Not-to-Shabby/TOMS/documentation/new_implementation_plan.md

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

---

## I. SLR Literature Analysis (TOMS.txt — Chapter II)

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

---

### A. Literature Challenges & TOMS Solutions

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

---

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

**TOMS approach — Real-time first, cache as fallback:**

```
Event occurs (NFC tap / payment / alarm)
        │
        ▼
  Internet available?
    YES ──► POST to server immediately (real-time occupancy)
    NO  ──► Write to local SQLite queue (synced = 0)
                    │
                    ▼
          Internet restored?
            YES ──► Flush SQLite queue (oldest first) + continue real-time
            NO  ──► Keep caching, retry every 30s
```

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

---

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

---

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

---

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

---

### B. Literature Research Gaps & TOMS Responses

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

---

### C. Occupancy — Does TOMS Align with the Literature?

**YES — and it fills the gap the literature couldn't.**

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

**TOMS fills this gap exactly:**

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

---

### D. Hardware Alignment with Literature (Table 2.9 / 2.10)

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

---

## II. Survey Problem Analysis & TOMS Solutions

The following maps each of the 7 identified field problems directly to TOMS features.

---

### Problem 1 — Inaccurate Passenger Counting
> *80% of conductors rely solely on memory or visual estimation*

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

---

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

**Root cause:** Conductors compute fares mentally while multitasking. Large bills create change-management stress.

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

---

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

---

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

**Root cause:** Paper tickets can be discarded. Verbal-only transactions leave no evidence.

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

---

### Problem 5 — Environmental Waste from Paper Tickets
> *90% agree paper tickets produce litter*

**Root cause:** Single-use paper tickets issued per passenger per trip.

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

---

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

**Root cause:** Routes pass through forested/rural areas with zero cellular signal.

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

---

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

**Root cause:** No digital record. Physical ticket collection is the only audit mechanism.

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

---

## II. Confirmed Architecture Decisions

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

---

## III. System Components

```
┌──────────────────────────────────────────────────────────────┐
│              COMPANY DASHBOARD (Web — browser)               │
│  Real-time fleet view, shift reports, audit trail, analytics │
│  Served from: Node.js or simple Python backend on office PC  │
│  Or: Static JSON export viewed in a local web app            │
└───────────────────────┬──────────────────────────────────────┘
                        │ Wi-Fi / USB sync (end of shift)
┌───────────────────────▼──────────────────────────────────────┐
│              FLUTTER APP (Conductor's Phone)                  │
│  Session mgmt • GPS • Fare calc • Proximity alarm            │
│  Offline SQLite log • Sync service                           │
└───────────────────────┬──────────────────────────────────────┘
                        │ USB CDC (always connected in-trip)
┌───────────────────────▼──────────────────────────────────────┐
│              ESP32 MASTER                                     │
│  NFC-DEP initiator (PN532) • ESP-NOW hub • SPIFFS backup    │
└────────────┬──────────────────────────────┬──────────────────┘
       NFC tap                          ESP-NOW
┌───────────▼──────────┐    ┌────────────▼──────────────────┐
│  SLAVE (NFC Target)  │    │  SLAVE (Button Press / Board) │
│  Shows QR receipt    │    │  PASSENGER_BOARD confirm      │
└──────────────────────┘    └───────────────────────────────┘
```

---

## IV. Occupancy Model

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

### Slot Number vs Seat Number

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

### Passenger States
```
ACTIVE    → BOARD_COMMAND sent, receipt on slave screen, payment pending
PAID      → passenger pressed button, fare collected, slave returned
ALARMING  → proximity alarm triggered, still unpaid
```

### Occupancy Flow
```
Trip starts. Bus has 0 slaves deployed. Capacity = 20.

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

Passenger 2 boards:
    → slot_number = 2
    → slavesDeployed = 2  →  Occupancy: 2/20 (10%)

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

GPS within 200m of Country Hills:
    → Slot 2 still unpaid → state = ALARMING
    → App banner + vibration
```

### `PassengerSlotState` enum (Flutter)
```dart
enum PassengerSlotState { active, paid, alarming }

extension PassengerSlotStateX on PassengerSlotState {
  Color get color => [
    const Color(0xFFFF9F43),   // active   → orange
    const Color(0xFF2ED573),   // paid     → green
    const Color(0xFFFF6B6B),   // alarming → red
  ][index];
  String get label => ['Unpaid', 'Paid', 'ALARM'][index];
}
```

### `OccupancySnapshot` (for dashboard sync)
```dart
class OccupancySnapshot {
  final String vehicleId;
  final DateTime timestamp;
  final int maxCapacity;          // configured max (e.g. 20)
  final int slavesDeployed;       // currently handed out
  final int paidCount;
  final int unpaidCount;
  final int alarmingCount;
  double get occupancyRate => slavesDeployed / maxCapacity;
  final List<PassengerSlot> slots;
}

class PassengerSlot {
  final int slotNumber;           // 1-based, order boarded
  final String slaveUid;          // eFuse MAC
  final PassengerSlotState state;
  final String destination;
  final int fareCentavos;
  final PassengerType passengerType;
  final DateTime boardedAt;
}
```

---

## V. Data Models

### `PassengerType` enum
```dart
enum PassengerType { regular, student, pwd, senior }

extension PassengerTypeX on PassengerType {
  String get label => ['Regular', 'Student', 'PWD', 'Senior'][index];
  double get multiplier => [1.0, 0.80, 0.80, 0.80][index];
}
```

### `TransitStop`
```dart
class TransitStop {
  final int id;
  final String name;
  final double lat;
  final double lon;
}
```
Loaded from `assets/stops.json` at startup.

### `PassengerSession`
```dart
class PassengerSession {
  final String id;              // UUID
  final String slaveUid;        // eFuse MAC of assigned slave
  final TransitStop boarding;
  final TransitStop destination;
  final int fareId;
  final int baseFareCentavos;
  final int finalFareCentavos;  // after discount
  final PassengerType type;
  final DateTime boardedAt;
  bool paid;
  bool alarmTriggered;
}
```

### `PendingPassenger` (Queue mode)
```dart
class PendingPassenger {
  final String id;
  final TransitStop boarding;
  final TransitStop destination;
  final int fareId;
  final int fareCentavos;
  final PassengerType type;
  final DateTime queuedAt;
}
```

### `PassengerLog` (updated)
```dart
// New fields added:
final int passengerType;        // PassengerType.index
final int discountCentavos;
final String boardingStop;
final String destinationStop;
final double destinationLat;
final double destinationLon;
```

### `DeviceStatus` (updated)
```dart
// Rename: uartState → nfcState
// Parse: json['nfc_state'] instead of json['uart_state']
final int nfcState;
```

### `ShiftReport` (new — for dashboard sync)
```dart
class ShiftReport {
  final String vehicleId;
  final String routeName;
  final DateTime shiftStart;
  final DateTime shiftEnd;
  final int totalPassengers;
  final int totalRevenueCentavos;
  final int regularCount;
  final int studentCount;
  final int pwdCount;
  final int seniorCount;
  final int discountTotalCentavos;
  final List<PassengerLog> transactions;
}
```

---

## V. Database Schema

**Version bump: `v1` → `v2`**

```sql
-- Migration from v1 to v2
ALTER TABLE passenger_logs ADD COLUMN passenger_type    INTEGER DEFAULT 0;
ALTER TABLE passenger_logs ADD COLUMN discount_centavos INTEGER DEFAULT 0;
ALTER TABLE passenger_logs ADD COLUMN boarding_stop     TEXT    DEFAULT '';
ALTER TABLE passenger_logs ADD COLUMN destination_stop  TEXT    DEFAULT '';
ALTER TABLE passenger_logs ADD COLUMN destination_lat   REAL    DEFAULT 0;
ALTER TABLE passenger_logs ADD COLUMN destination_lon   REAL    DEFAULT 0;
```

---

## VI. New Assets

### `assets/stops.json`
```json
[
  {"id":1, "name":"DPWH - Tambo Terminal",       "lat":8.2287, "lon":124.2451},
  {"id":2, "name":"Country Hills",               "lat":8.2456, "lon":124.2611},
  {"id":3, "name":"Brgy. Burul",                 "lat":8.2378, "lon":124.2534},
  {"id":4, "name":"Tag-ibo",                     "lat":8.1912, "lon":124.2133},
  {"id":5, "name":"Dalipuga Terminal",            "lat":8.1756, "lon":124.2089}
]
```
Operator populates the actual coordinates before deployment.

---

## VII. Services (Flutter)

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

### `SyncService` — Detailed Behaviour

```dart
class SyncService {
  // Called after every boarding event, payment, or alarm
  Future<void> push(OccupancyEvent event) async {
    // 1. Save to SQLite immediately (synced = 0)
    await _db.insertEvent(event);

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

  // Retry every 30 seconds while offline
  void startRetryTimer() {
    Timer.periodic(Duration(seconds: 30), (_) {
      if (_connectivity.isOnline) flushQueue();
    });
  }
}
```

**What is pushed to the server on each event:**
```json
{
  "event_type": "board",          // board | payment | alarm | release
  "timestamp": "2026-05-26T21:05:33+08:00",
  "vehicle_id": "CDB-001",
  "route": "Dalipuga",
  "slot_number": 3,
  "slave_uid": "A1B2C3D4E5F6",
  "passenger_type": "senior",
  "fare_centavos": 1040,
  "discount_centavos": 260,
  "boarding_stop": "DPWH Terminal",
  "destination_stop": "Country Hills",
  "occupancy_now": 14,             // slavesDeployed at time of event
  "max_capacity": 20
}
```

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

**Connectivity state indicator in UI:**
```
  🟢 Online   — events sent live to dashboard
  🟡 Caching  — N events queued, will sync on reconnect
  🔴 No USB   — master disconnected
```

### Discount Calculation
```dart
int calculateFare(int baseFareCentavos, PassengerType type) {
  return (baseFareCentavos * type.multiplier).ceil();
}
int calculateDiscount(int baseFareCentavos, PassengerType type) {
  return baseFareCentavos - calculateFare(baseFareCentavos, type);
}
```

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

---

## IX. Screens (Flutter App)

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

### New: `OccupancyPanel` (embedded in Dashboard, main widget)

No grid/seat map — just a capacity bar and a list of active passenger slot cards:
```
  CDB-001 · Dalipuga Route
  ┌────────────────────────────────────────────┐
  │ Occupancy  ████████████░░░░░░░░  14 / 20  │
  │            Unpaid: 3   Paid: 11   70%      │
  └────────────────────────────────────────────┘

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

  [ + New Passenger ]   Revenue today: ₱271.80
```

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

### New: `BoardingSheet` (Modal bottom sheet, 2 tabs)

**Tab 1 — Quick (Sequential)**
```
Boarding Point
  ○ Auto-GPS: [DPWH Terminal ✓ — detected]
  ○ Manual:   [Select stop ▾]

Destination:  [Country Hills ▾]
Passenger:    [Regular ▾]     → Fare: ₱13.00
                               → Discount: —

[Tap Slave via NFC]
```
- Auto-GPS pre-fills boarding stop from nearest stop to current phone position
- Selecting "Manual" shows the stop picker (searchable list)

**Tab 2 — Queue (Multi-passenger)**
```
Pending Queue
  □ DPWH → Country Hills  ₱13.00  Regular    [Assign →]
  □ DPWH → Brgy. Burol   ₱10.00  Senior ★   [Assign →]

[+ Add Another Passenger]
```
- "Assign →" taps that queue item's slave via NFC
- Multiple passengers can be queued before any slave is assigned

### New: `ActiveSessionsPanel` (on dashboard)
```
ACTIVE PASSENGERS  (3 riding · 2 unpaid)
┌─────────────────────────────────────────────────────┐
│ 🔴 S2  Country Hills    ₱10.40 Senior    UNPAID ⚠  │  ← alarm near
│ 🟡 S1  Brgy. Burol     ₱10.00 Regular   UNPAID    │
│ ✅ S3  Tambo Terminal  ₱ 9.00 Student   PAID      │
└─────────────────────────────────────────────────────┘
```
Each row: tap to expand → shows boarding time, slave UID, change calc

### New: `ProximityAlarmBanner`
```
⚠ UNPAID FARE — 150m to Country Hills
   Slave S2 · ₱10.40 Senior Citizen
                                    [Mark Paid]  [Dismiss]
```
+ Phone vibration + local notification sound

### New: `ShiftSummaryScreen`
Accessible from the overflow menu. Shows end-of-shift stats:
```
SHIFT SUMMARY  —  May 26, 2026

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

[ Export JSON ]   [ Sync to Dashboard ]
```

---

## IX. Company Dashboard (Web)

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

### Dashboard Screens

#### 1. Fleet Overview (Home) — with Live Occupancy
```
TOMS Fleet Dashboard — DATRANSCO                  May 26, 2026

Active Buses: 3    Fleet Avg Occupancy: 61%    Total Revenue Today: ₱4,230.00

┌──────────┬──────────┬───────────┬──────────────────────┬──────────┬──────────┐
│ Bus ID   │ Route    │ Conductor │ Occupancy            │ Revenue  │ Status   │
├──────────┼──────────┼───────────┼──────────────────────┼──────────┼──────────┤
│ CDB-001  │ Dalipuga │ J. Reyes  │ ████████░░  14/20    │ ₱168.00  │ 🟢 Live  │
│ CDB-002  │ Dalipuga │ R. Santos │ █████░░░░░   9/20    │ ₱109.00  │ 🟡 Sync  │
│ CDB-003  │ Buru-un  │ M. Cruz   │ ████████████ 20/20   │ ₱240.00  │ 🟢 Live  │
└──────────┴──────────┴───────────┴──────────────────────┴──────────┴──────────┘
```
- **Occupancy** = slaves deployed / bus max capacity
- **🟢 Live** = events received in real-time (phone has internet)
- **🟡 N cached** = phone offline, N events queued — occupancy shown is last known state
- Click any row → opens per-bus **passenger slot list** (mirrors conductor's phone panel)
- `20/20` (FULL) highlighted — dispatcher knows to send the next bus
- Occupancy updates immediately as events arrive; no manual refresh needed

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

#### 3. Revenue Analytics
```
Revenue Trends — Last 7 Days

₱5,000 ┤                              ╭───╮
₱4,000 ┤              ╭──╮           │   │
₱3,000 ┤    ╭──╮     │  ╰──╮       ╭╯   ╰─
₱2,000 ┤───╯  ╰─────╯     ╰──────╯
       Mon   Tue   Wed   Thu   Fri   Sat   Sun

Passenger Type Breakdown:
  Regular  78%   ████████████████████░░░░░
  Student  12%   ████░░░░░░░░░░░░░░░░░░░░░
  Senior    7%   ██░░░░░░░░░░░░░░░░░░░░░░░
  PWD       3%   █░░░░░░░░░░░░░░░░░░░░░░░░
```

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

#### 5. Reconciliation Report (replaces the 6 PM office visit)
```
End-of-Day Reconciliation — May 26, 2026

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

Bus CDB-002 (Buru-un):
  Expected passengers:  18
  Expected revenue:   ₱214.50
  Cash declared:      ₱200.00  ⚠ DISCREPANCY: -₱14.50
  Status: ❌ REVIEW REQUIRED
```

### Dashboard Tech Stack Options

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

---

## X. Flutter Packages Required

```yaml
# pubspec.yaml additions
geolocator: ^13.0.1              # Phone GPS
permission_handler: ^11.3.0      # Location + notification permissions
vibration: ^3.1.2                # Haptic alarm
flutter_local_notifications: ^17.2.2  # Audible alarm
share_plus: ^10.0.2              # Export shift JSON / CSV
http: ^1.2.0                     # Real-time event POST + sync queue flush
uuid: ^4.4.0                     # Session ID generation
connectivity_plus: ^6.0.3        # Internet state monitoring (online/offline)
```

---

## XI. Protocol Extension (Firmware, Phase 4 Only)

### New: `TOMS_MSG_ALARM_CMD` (Master → Slave)

Add to `shared_lib/protocol/protocol.h`:
```c
TOMS_MSG_ALARM_CMD = 0x30,

typedef struct __attribute__((packed)) {
    uint8_t  target_uid[16];
    uint8_t  alarm_type;      // 0 = proximity warning, 1 = final stop
    uint8_t  minutes_left;
} toms_alarm_cmd_t;
```

Master USB handler — new command from phone:
```json
{"cmd":"send_alarm", "uid":"A1B2C3D4E5F6", "alarm_type":0, "minutes":2}
```

Slave response: Flash screen red → "Please Pay — 2 min to stop"

---

## XIII. Build Phases

### Phase 1 — NFC + Occupancy Foundation (Flutter only)
- [ ] Update `DeviceStatus`: `uartState` → `nfcState`
- [ ] Add `PassengerType`, `TransitStop`, `PassengerSession`, `PendingPassenger` to models
- [ ] Add `SeatState`, `SeatRecord`, `OccupancySnapshot` to models
- [ ] Add `NfcTapEvent` model
- [ ] Database v2 migration (add columns)
- [ ] `OccupancyService` — seat state table, update from NFC tap + button_press + proximity
- [ ] `SessionService` (sessions + queue + fare calc + discounts)
- [ ] `UsbService` NFC event handlers (replace dock with nfc/nfc_tap)
- [ ] `AppState` wired to OccupancyService + SessionService + button_press → markPaid

### Phase 2 — Occupancy Panel + Boarding UI
- [ ] `assets/vehicles.json` — max capacity per bus ID (simple: `{"CDB-001": 20, ...}`)
- [ ] `assets/stops.json` (named stops + GPS coords)
- [ ] `StopService` (load + find nearest stop)
- [ ] **`OccupancyPanel`** — capacity bar + `PassengerSlot` card list, embedded in Dashboard
- [ ] Slot number auto-increment logic in `SessionService` (resets each trip)
- [ ] [Release Slave] action → frees slot, slave returned to pool
- [ ] `BoardingSheet` — Quick tab (GPS auto-boarding + stop picker + discount selector)
- [ ] `BoardingSheet` — Queue tab (multi-passenger queue)
- [ ] `ShiftSummaryScreen` with occupancy stats (peak occupancy, avg load, etc.)
- [ ] NFC tap → BOARD_COMMAND with `slot_number` (reused `seat_number` field) + fare + type

### Phase 3 — GPS + Proximity Alarm
- [ ] `GpsService` with `geolocator`
- [ ] `ProximityService` — 200m geofence, updates seat state to ALARMING
- [ ] Seat map tile pulses red when ALARMING
- [ ] `ProximityAlarmBanner` with [Mark Paid] action
- [ ] Vibration + local notification
- [ ] Android permissions: `ACCESS_FINE_LOCATION`, `VIBRATE`, `POST_NOTIFICATIONS`

### Phase 4 — Company Dashboard + Sync
- [ ] `SyncService` — export `OccupancySnapshot` + `ShiftReport` JSON
- [ ] Company dashboard (HTML/JS)
  - Fleet overview with live occupancy bars per bus
  - Per-bus seat map view (mirrors conductor's phone)
  - Transaction audit log (searchable)
  - Revenue analytics (per day/week, passenger type breakdown)
  - Reconciliation report (auto-flags discrepancy)
  - Dispute resolution search by UID / timestamp
- [ ] `share_plus` — conductor shares shift JSON at terminal

### Phase 5 — Slave Alarm (Firmware, Optional)
- [ ] `TOMS_MSG_ALARM_CMD` in `protocol.h`
- [ ] Slave: alarm cmd → red screen + "Please Pay" UI
- [ ] Master: `send_alarm` USB cmd → ESP-NOW to target slave
- [ ] Flutter `ProximityService` triggers slave alarm alongside phone alarm
