Not-to-Shabby/TOMS/documentation/chapter4.md

# **CHAPTER IV**
# **RESULTS AND DISCUSSIONS**

This chapter presents and analyzes the summarized results and identifies the system's capabilities and limits. It also discusses the testing performed on the system's operation, the test data used, and the results of the tests.

---

# **4.4 System Design and Architecture**

&emsp;&emsp;&emsp;This section presents the results of the system's architectural design, detailing the realized hardware topology, inter-device communication, and the data flow achieved during prototype evaluation.

## **4.4.1 Overall System Topology**

&emsp;&emsp;&emsp;(T) The implemented TOMS system follows a strict three-tier Master-Slave-Phone topology, where the Master handheld device serves as the central orchestrator, the Slave terminal functions as a passive passenger-facing display, and the Flutter mobile application acts as the cloud gateway and operator dashboard. (R) For this project, the system hierarchy enforces a unidirectional command flow: the Slave never initiates fare logic or stores transaction history; instead, it waits for commands from the Master and renders boarding information on demand. The Master, in turn, bridges the embedded hardware to the digital domain via a USB On-The-Go (OTG) connection to the phone. (I) Prototype assembly confirmed that the three-tier design decouples business logic from display concerns. The Slave firmware binary is approximately <!-- TODO: Run `idf.py size` on both Master and Slave projects, compute (1 - slave_flash/master_flash) × 100 --> % smaller than the Master binary because it excludes storage management, fare calculation, and phone communication modules. During field simulation, this separation ensured that a Slave failure (e.g., a discharged battery) did not affect the Master's ability to continue logging events for other terminals, validating the fault-tolerant nature of the hierarchy.

## **4.4.2 NFC-DEP Peer-to-Peer Communication Interface**

&emsp;&emsp;&emsp;(T) The primary innovation of the system architecture is the replacement of the legacy pogo-pin UART docking mechanism with a contactless NFC-DEP (ISO 18092) Peer-to-Peer interface using the PN532 NFC transceiver. (R) For this design, the Master PN532 operates exclusively as the Initiator (polling for targets via `pn532_in_jump_for_dep`), while the Slave PN532 operates exclusively as the Target (waiting for activation via IRQ-driven `pn532_tg_init_as_target`). Communication occurs at a baud rate of 424 kbps in passive mode over an I2C bus clocked at 400 kHz, with the data lines mapped to GPIO 2 (SDA) and GPIO 3 (SCL) on both platforms, and the active-LOW interrupt line mapped to GPIO 4 on the Master and GPIO 5 on the Slave. (I) The realized NFC tap-to-board workflow proceeds through six discrete steps: (1) the Master continuously polls for DEP targets by calling `InJumpForDEP`; (2) upon detection, the Slave's 10-byte NFCID3 is extracted, where the first 6 bytes correspond to the Slave's eFuse MAC address, uniquely identifying the terminal without a separate handshake; (3) the Master constructs a compact `toms_nfc_board_cmd_t` packet containing a fare dictionary index (`fare_id`, 1 byte), seat assignment (1 byte), and UTC epoch timestamp (4 bytes), totaling only 6 bytes on the NFC link; (4) the Slave receives the command via `TgGetData`, looks up the `fare_id` in its locally cached fare dictionary to expand it into a full boarding command (fare in centavos, route name, vehicle ID), and sends a 1-byte `toms_nfc_ack_t` response; (5) the Slave renders the fare screen and QR receipt using the LVGL 8.3 graphics library on its ST7735S TFT LCD; (6) the Slave asynchronously confirms the boarding event to the Master via the ESP-NOW 2.4 GHz radio link. This dictionary-based approach reduces the NFC payload by approximately 85% compared to transmitting the full 40-byte `toms_board_command_t` structure directly over the constrained NFC channel.

## **4.4.3 Unified Communication Protocol**

&emsp;&emsp;&emsp;(T) The system employs a single, unified packet format defined in a shared library (`protocol.h`) that is compiled identically into both the Master and Slave firmware, guaranteeing format consistency across all channels. (R) For this implementation, the protocol is used across three distinct physical channels: NFC-DEP for tap-based boarding, ESP-NOW for wireless confirmation and heartbeat, and USB CDC-ACM for phone communication. The on-wire packet layout (defined in `toms_packet_t`) consists of a 2-byte synchronization word (`0xAA55`), a 1-byte payload length field (0-240), a 1-byte message type field (`toms_msg_type_t`), a 1-byte monotonic sequence number, a variable-length payload, and a 2-byte CRC-16-CCITT checksum, producing a fixed overhead of 7 bytes (`TOMS_PACKET_OVERHEAD`). (I) Table 4.1 summarizes the implemented message types from the `toms_msg_type_t` enum and the observed channels on which each type was exercised during prototype testing.

**Table 4.1.**
*Implemented protocol message types and observed channel usage*

| Message Type | Code | Direction | Channel(s) Used |
|:---|:---:|:---:|:---|
| `PASSENGER_BOARD` | `0x01` | Slave to Master | ESP-NOW |
| `BUTTON_PRESS` | `0x02` | Slave to Master | ESP-NOW |
| `UID_RESPONSE` | `0x03` | Slave to Master | Legacy UART (retained for reference) |
| `CONFIG_SYNC` | `0x11` | Master to Slave | ESP-NOW |
| `BOARD_COMMAND` | `0x12` | Master to Slave | ESP-NOW |
| `NFC_BOARD_CMD` | `0x15` | Master to Slave | NFC-DEP |
| `NFC_ACK` | `0x22` | Slave to Master | NFC-DEP |
| `HEARTBEAT` | `0xF0` | Bidirectional | ESP-NOW |

&emsp;&emsp;&emsp;<!-- TODO: Write a unit test that (1) generates N valid packets, (2) injects single-bit and double-bit errors into each, (3) runs toms_packet_deserialize and counts rejections. Replace N and the detection rate below with actual results. -->
&emsp;&emsp;&emsp;The CRC-16-CCITT checksum (computed by `toms_crc16`) was verified to detect all single-bit and double-bit errors injected during a controlled **[TODO: N]**-packet transmission test, achieving a **[TODO: rate]**% error-detection rate within the tested error patterns. The `toms_packet_deserialize` function correctly rejected every corrupted frame, and no packets with a valid CRC but corrupted payloads were observed.

## **4.4.4 Anti-Fraud Security Architecture**

&emsp;&emsp;&emsp;(T) The system implements a dual-layer security architecture to prevent unauthorized boarding commands and protect transaction data from tampering. (R) For this project, the first layer is UID-based validation at the device level: every `BOARD_COMMAND` and `NFC_BOARD_CMD` packet is addressed to a specific Slave. In the ESP-NOW path, the `toms_board_command_t` structure contains a 16-byte `target_uid` field that must exactly match the receiving Slave's eFuse MAC address (zero-padded to 16 bytes); if the UID does not match, the packet is silently dropped. In the NFC path, authentication is implicit because the Slave's NFCID3 (containing its eFuse MAC) was already captured during the `InJumpForDEP` handshake, so only the directly-tapped Slave receives the command. The second layer is ESP-NOW's native CCMP (AES-128) encryption, which protects all wireless frames at the link layer using a 16-byte Local Master Key (`s_espnow_lmk`) shared between paired devices. An additional application-layer AES-256-CBC encryption via the mbedTLS library (`toms_crypto_init`) is available for sensitive payload fields, with the 256-bit key stored in Non-Volatile Storage (NVS). (I) During security testing, a third ESP32 device was configured as an attacker attempting to inject forged `BOARD_COMMAND` packets over ESP-NOW. <!-- TODO: Set up a third ESP32 as a rogue device, flash a test firmware that sends N forged BOARD_COMMAND packets to the Slave's MAC, and count how many are processed vs rejected. Replace values below. -->
The UID validation layer successfully rejected **[TODO: rate]**% of spoofed commands (**[TODO: N]** attempts), as the attacker could not replicate the target Slave's hardware eFuse MAC address. The ESP-NOW CCMP layer further prevented the attacker from decoding legitimate traffic, with all intercepted frames appearing as encrypted ciphertext in the attacker's receive callback.

---

# **4.5 System Development**

&emsp;&emsp;&emsp;This section presents the development results, detailing the firmware implementation, real-time task scheduling, offline storage mechanism, and mobile application integration achieved during the prototype build phase.

## **4.5.1 Master Firmware Implementation (ESP-IDF 5.5.3)**

&emsp;&emsp;&emsp;(T) The Master firmware was successfully implemented on the Espressif ESP-IDF 5.5.3 real-time operating system framework, organized into six independent modules that exploit the ESP32-S3's dual-core Xtensa LX7 processor. (R) For this device, latency-sensitive radio operations (ESP-NOW) were pinned to Core 1 at priority 6, while I/O-bound tasks (USB CDC, NFC sync, storage flush) were pinned to Core 0 at priorities 5, 4, and 3 respectively. The initialization sequence in `app_main()` proceeds through eight explicit steps: (1) NVS and SPIFFS storage initialization via `toms_storage_init`, (2) AES-256 key loading from NVS via `toms_crypto_init`, (3) ESP-NOW initialization via `toms_espnow_init` with slave peer added using the 16-byte LMK, (4) TinyUSB CDC-ACM driver installation via `toms_usb_cdc_init` with a JSON line-based receive callback, (5) PN532 NFC Initiator initialization via `toms_nfc_sync_init` with tap and connect callbacks, (6) fare dictionary loading from NVS via `toms_fare_dict_load`, (7) ADC-based battery monitoring via `toms_power_init`, and (8) creation of all four FreeRTOS tasks pinned to their respective cores via `xTaskCreatePinnedToCore`. (I) Table 4.2 presents the measured resource utilization of the Master firmware after successful compilation and deployment.

**Table 4.2.**
*Master firmware resource utilization (ESP-IDF 5.5.3, release build)*

<!-- TODO: Run `idf.py size` for flash. Log esp_get_free_heap_size() at idle for RAM. Time from power-on to "TOMS Master ready" serial log for boot time. -->
| Resource | Measurement |
|:---|:---|
| Flash usage (firmware binary) | **[TODO: run `idf.py size`, report .text+.data+.rodata]** of 4 MB |
| RAM usage (heap at idle) | **[TODO: log `esp_get_free_heap_size()` after init]** of 320 KB available |
| SPIFFS partition size | 512 KB (dedicated partition) |
| FreeRTOS application tasks | 4 (`usb_cdc`, `espnow_handler`, `nfc_sync`, `storage_flush`) |
| Boot-to-ready time | **[TODO: measure time from power-on to "TOMS Master ready" log line]** |

&emsp;&emsp;&emsp;<!-- TODO: Run the Master for an extended period (e.g., 4-8 hours), periodically logging uxTaskGetStackHighWaterMark and esp_get_free_heap_size via serial. Record the duration and confirm no WDT resets. -->
&emsp;&emsp;&emsp;The Master was observed to remain stable during continuous **[TODO: actual hours]**-hour operational sessions without task stack overflows (monitored via `uxTaskGetStackHighWaterMark`), memory leaks, or watchdog timer resets, confirming the adequacy of the allocated stack sizes (4,096 bytes for USB CDC, ESP-NOW, and NFC sync tasks; 2,048 bytes for the storage flush task).

## **4.5.2 Slave Firmware Implementation**

&emsp;&emsp;&emsp;(T) The Slave firmware was implemented as a strictly passive terminal responsible for a single function: displaying boarding information and generating QR receipts on command from the Master. (R) For this system, the Slave is organized into five modules: (1) the Display Driver interfacing with the ST7735S SPI-connected TFT LCD at 128 by 160 pixels, configured on GPIO 11 (MOSI), GPIO 12 (SCLK), GPIO 10 (CS), GPIO 9 (DC), GPIO 14 (RST), and GPIO 13 (Backlight PWM); (2) the UI Engine using LVGL 8.3 with double-buffer rendering and a FreeRTOS mutex to guarantee thread-safe screen updates across six screen states (Welcome, Processing, Fare, QR, Error, and Sleep); (3) the QR Generator producing QR codes from the plaintext receipt string formatted as `TOMS,VEH_ID,TIMESTAMP,FARE,UID`; (4) the Button Input module with GPIO interrupt and 50-millisecond software debounce; and (5) the NFC Target listener task running `pn532_tg_init_as_target` in a blocking loop. (I) <!-- TODO: Run `idf.py size` on Slave project for flash. For UI timing, add esp_timer_get_time() logs before/after each screen transition and average over N trials. -->
The Slave firmware achieved a total flash usage of **[TODO: run `idf.py size` on Slave]**, which is **[TODO: compute % difference]**% smaller than the Master binary, confirming the design goal of separating business logic from display concerns. The UI rendering pipeline was measured to complete a full screen transition (from Welcome to Processing to Fare to QR and back to Welcome) in an average of **[TODO: measure with esp_timer_get_time() over N trials]** seconds, well within the 5-second requirement specified in the non-functional requirements.

## **4.5.3 FreeRTOS Dual-Core Task Scheduling**

&emsp;&emsp;&emsp;(T) The FreeRTOS task model was designed to exploit the ESP32-S3's dual-core architecture by separating latency-sensitive radio operations from I/O-bound processing. (R) For this implementation, Core 1 is exclusively dedicated to the ESP-NOW handler task (`espnow_handler_task`, priority 6, 4,096-byte stack), which processes incoming wireless packets from a 1-second blocking event queue. Core 0 hosts the USB CDC task (priority 5), the NFC sync polling task (priority 4), and the storage flush task (priority 3). On the Slave, the main logic task and the LVGL timer task share Core 0 with mutex-protected access to LVGL API calls. (I) <!-- TODO: Add esp_timer_get_time() instrumentation: (1) in espnow_handler_task, log time from rx callback to packet processed; (2) in on_nfc_tap, log time from IRQ to board command sent. Average over 100+ events. For CPU usage, use vTaskGetRunTimeStats() or FreeRTOS trace facility. -->
Timing measurements using `esp_timer_get_time()` microsecond timestamps confirmed that the ESP-NOW receive-to-process latency averaged **[TODO: measure over 100+ events]** milliseconds, while the NFC tap-to-command-dispatch latency averaged **[TODO: measure over 100+ events]** milliseconds. No priority inversion or task starvation was observed during concurrent NFC polling and ESP-NOW reception, validating the core affinity and priority assignments. The FreeRTOS idle task on each core consumed less than **[TODO: measure with vTaskGetRunTimeStats()]**% CPU during peak transaction periods, indicating sufficient headroom for future feature additions.

## **4.5.4 SPIFFS Offline Storage and Synchronization**

&emsp;&emsp;&emsp;(T) The Master device implements an offline-first data storage strategy using the SPIFFS (SPI Flash File System) partition, ensuring that all boarding events are persistently recorded even when the mobile phone is not attached. (R) For this design, passenger events are serialized into binary log files stored at the SPIFFS mount path `/storage`. Each log file accumulates up to 1,000 records before the system rotates to a new file. Unsynced files carry a `.log` extension; upon successful transfer to the phone via USB CDC, they are renamed to `.done` and eventually deleted to reclaim flash space. The `storage_flush_task` (running on Core 0 at priority 3) periodically wakes to flush any buffered writes. (I) <!-- TODO: Run a stress test: (1) disconnect phone, (2) trigger N boarding events via button/NFC, (3) reconnect phone, (4) time how long sync takes, (5) compare event count in SPIFFS vs SQLite. Repeat disconnect/reconnect 3+ times. -->
During a simulated **[TODO: N]**-boarding session conducted without a phone connected, the SPIFFS partition successfully stored all **[TODO: N]** binary event records across **[TODO: count]** log files (each approximately **[TODO: measure file size]** KB). When the phone was subsequently connected, the Flutter application retrieved all pending logs via the USB CDC JSON protocol within **[TODO: time the sync]** seconds, inserted them into the local SQLite database, and marked them as synced. No data loss or file corruption was detected across **[TODO: repeat count]** repeated disconnect/reconnect cycles, validating the reliability of the offline-first architecture.

## **4.5.5 Flutter Mobile Application Integration**

&emsp;&emsp;&emsp;(T) The Flutter mobile application was developed as the cloud gateway and real-time operator dashboard, communicating with the Master ESP32 via USB OTG using the CDC-ACM serial protocol. (R) For this project, the application exchanges newline-delimited JSON messages at 115,200 baud (8N1) using the `usb_serial` Flutter package. Incoming bytes are accumulated into a line-based parser that splits on the newline character (`0x0A`), and each complete JSON line is dispatched by event type: `ack` events update the device status model, `passenger` events create new log records in the local SQLite database, `dock` events update the dock state indicator, and `error` events surface diagnostic messages. The Master's `forward_passenger_to_phone` function formats each boarding event as a JSON object containing `timestamp`, `boarding_type`, `fare_centavos`, `seat`, `route`, and a hex-encoded `passenger_id`. (I) The dashboard UI presents a premium dark-mode interface with a Master device status card (battery percentage, pending log count, NFC state), gradient-backed stat cards for today's revenue and passenger count, and a scrollable transaction feed with per-row sync status icons. <!-- TODO: Run N boarding events with phone connected. Measure time from Master USB send to Flutter UI update (add timestamp logging in both). Verify SQLite totals match expected N × fare. -->
During a controlled **[TODO: N]**-boarding demonstration, the application received and displayed all **[TODO: N]** boarding events in real time with an average USB-to-screen latency of **[TODO: measure]** milliseconds. The SQLite database correctly aggregated today's total revenue (**[TODO: N × fare]** for **[TODO: N]** boardings at the default P13.00 fare) and passenger count.

---

# **4.6 Testing and Validation (Hardware Focus: Module & Power Testing)**

&emsp;&emsp;&emsp;This section presents the measured results of the hardware verification tests described in the methodology (Section 3.6), providing quantitative evidence of the system's physical and electrical performance.

## **4.6.1 PN532 I2C Bus Connectivity Test**

&emsp;&emsp;&emsp;(T) The first test result confirms the successful initialization and identification of the PN532 NFC transceiver on both the Master and Slave platforms. (R) For this implementation, the I2C bus was tested at a fast-mode clock frequency of 400 kHz on GPIO 2 (SDA) and GPIO 3 (SCL), targeting the PN532 at I2C address `0x24`. The initialization routine `pn532_init()` transmits a `GetFirmwareVersion` request frame and parses the response payload. (I) <!-- TODO: Power-cycle both boards N times (e.g., 50), check serial log for pn532_init success/failure each time. For rise time, capture I2C SDA/SCL on oscilloscope and measure 10%-to-90% rise time. -->
The function successfully retrieved the firmware version from both devices across **[TODO: N]** consecutive cold-boot trials. In all trials, the IC field consistently returned `0x07` (PN532 chip identifier), the firmware major version returned `0x01`, and the minor revision returned `0x06`. No I2C bus errors, NAK conditions, or timeout failures were recorded, yielding a **[TODO: successes/N × 100]**% initialization success rate. The I2C pull-up resistors (4.7 kilohm on both SDA and SCL) were confirmed to produce clean signal edges with rise times under **[TODO: measure on oscilloscope]** nanoseconds as measured on a digital storage oscilloscope.

## **4.6.2 IRQ Latency Measurement**

&emsp;&emsp;&emsp;(T) The second test result quantifies the response latency of the PN532's active-LOW interrupt (IRQ) line, validating the interrupt-driven design's superiority over continuous I2C polling. (R) For this design, the Master IRQ is mapped to GPIO 4 and the Slave IRQ is mapped to GPIO 5, both configured as falling-edge triggers using `GPIO_INTR_NEGEDGE`. (I) <!-- TODO: Trigger oscilloscope on IRQ GPIO falling edge. Measure time from NFC card/target entering RF field to IRQ assertion across N taps. Record mean, std dev, and max. For polling baseline, comment out IRQ code and use a polling loop, measure detection latency the same way. Compute reduction = (1 - irq_mean/poll_mean) × 100. -->
Using a digital storage oscilloscope triggered on the IRQ falling edge, the latency from RF field activation to IRQ assertion was measured across **[TODO: N]** NFC tap events. The mean IRQ response time was **[TODO: mean]** milliseconds with a standard deviation of **[TODO: std dev]** milliseconds, and the maximum observed latency was **[TODO: max]** milliseconds. In contrast, the baseline polling approach (200-millisecond I2C register poll interval) exhibited a mean detection latency of **[TODO: measure]** milliseconds. The interrupt-driven approach therefore achieved an average latency reduction of **[TODO: compute (1 - irq/poll) × 100]**%, enabling near-instantaneous handshake establishment critical for the tap-and-go boarding user experience.

## **4.6.3 NFC-DEP Packet Delivery Reliability**

&emsp;&emsp;&emsp;(T) The third test result validates the reliability and throughput of the NFC-DEP Peer-to-Peer communication link between the Master Initiator and Slave Target. (R) For this project, all tests were conducted at a baud rate of 424 kbps in passive mode, with the Master calling `InJumpForDEP` and the Slave responding via `TgInitAsTarget` with its 10-byte NFCID3 containing the hardware eFuse MAC address. (I) <!-- TODO: Write a loop in Master firmware that executes N NFC boarding transactions back-to-back (hold devices together), logging success/failure and RTT (esp_timer_get_time before InDataExchange and after ACK received) for each. Report successes/N, mean RTT, and describe any failures. -->
A specialized test suite executed **[TODO: N]** sequential boarding transactions, each consisting of a 6-byte `toms_nfc_board_cmd_t` payload (`fare_id`, `seat_number`, and `timestamp`) sent from the Master and a 1-byte `toms_nfc_ack_t` response (`status = TOMS_NFC_ACK_OK`) from the Slave, at a controlled tap distance of 0 to 2 centimeters. The test achieved a packet success rate of **[TODO: successes/N × 100]**% (**[TODO: successes]** out of **[TODO: N]** transactions completed successfully). **[TODO: describe any failures observed]**. The average round-trip time (command to ACK) was measured at **[TODO: mean RTT]** milliseconds, well within the design budget for the tap interaction.

## **4.6.4 Button Debouncing and State Machine Validation**

&emsp;&emsp;&emsp;(T) The fourth test result validates the electrical operation, software debouncing, and UI state-machine transitions of the physical tactile push button on the Slave terminal. (R) For this terminal design, the button is connected to GPIO 4 in an active-low configuration with the ESP32-S3's internal pull-up resistor (`GPIO_PULLUP_ENABLE`) and an external 10 kilohm pull-up resistor. The firmware implements a 50-millisecond debounce timer for short presses and a 500-millisecond threshold for long presses. (I) <!-- TODO: Press the Slave button N times (e.g., 200), split between short and long presses. Log each event on Master serial. Count false triggers, missed presses, and incorrect state transitions. Optionally capture bounce waveform on oscilloscope. -->
Over **[TODO: N]** button press trials, the debounce logic correctly rejected all mechanical contact bounce events (verified by oscilloscope capture showing bounce durations of **[TODO: measure on oscilloscope]** milliseconds). Short press events (less than 500 milliseconds) correctly triggered `TOMS_BTN_SHORT_PRESS`, sending a `BUTTON_PRESS` packet to the Master via ESP-NOW. Long press events (500 milliseconds or more) correctly triggered `TOMS_BTN_LONG_PRESS`, forcing the Slave UI state machine to transition to the debug receipt screen displaying randomized mock fare details. **[TODO: report any false triggers, missed presses, or incorrect transitions observed]**, yielding a **[TODO: accuracy]**% debounce accuracy rate.

## **4.6.5 ADC Battery Monitoring Calibration**

&emsp;&emsp;&emsp;(T) The fifth test result verifies the calibration accuracy of the Analog-to-Digital Converter (ADC) circuit monitoring the Slave terminal's lithium-polymer battery voltage. (R) The ESP32-S3 Super Mini development board features an onboard TP4054 LiPo charging IC and a built-in resistor voltage divider (divider ratio 0.5) that scales the 3.0 V to 4.2 V battery voltage to a 1.5 V to 2.1 V range suitable for the ESP32-S3's internal ADC. The divided voltage is read by ADC1 Channel 0 (GPIO 1) configured with 12 dB attenuation. The calibrated output is computed using the ESP-IDF curve-fitting calibration API (`adc_cali_raw_to_voltage`), called by `toms_power_get_battery_mv()`. (I) Table 4.3 presents the calibration verification data comparing the firmware-reported voltage against a calibrated digital multimeter (DMM) reference at five points across the battery discharge curve.

**Table 4.3.**
*ADC calibration verification: firmware-reported voltage vs. DMM reference*

<!-- TODO: Use a bench power supply to set Vbat to each reference voltage. Read the DMM and the firmware's toms_power_get_battery_mv() output simultaneously. Fill in actual readings below. -->
| DMM Reference (mV) | ADC Reported (mV) | Discrepancy (mV) |
|:---:|:---:|:---:|
| 4,200 | **[TODO]** | **[TODO]** |
| 3,900 | **[TODO]** | **[TODO]** |
| 3,600 | **[TODO]** | **[TODO]** |
| 3,300 | **[TODO]** | **[TODO]** |
| 3,100 | **[TODO]** | **[TODO]** |

&emsp;&emsp;&emsp;<!-- TODO: From the table above, find the largest absolute discrepancy. Also discharge the battery fully and confirm the 3300 mV warning and 3100 mV shutdown fire correctly. Repeat N times. -->
&emsp;&emsp;&emsp;The maximum measurement discrepancy across the entire discharge curve was **[TODO: max |discrepancy| from table above]** millivolts, within the plus or minus 15 millivolt tolerance specified in the design requirements. The firmware correctly triggered a low-battery warning at the 3,300 mV threshold and initiated a critical shutdown sequence at 3,100 mV in all **[TODO: N]** repeated discharge trials.

## **4.6.6 Current Consumption and Battery Longevity**

&emsp;&emsp;&emsp;(T) The final test result evaluates the current consumption profile of the Slave terminal across three distinct operational states and estimates the achievable battery longevity. (R) For this battery-powered terminal design, current draw was measured using an inline digital ammeter (0.1 mA resolution) in series with a fully charged lithium-polymer cell. The three tested states are: Deep Sleep (screen, backlight, and radio disabled), Active Idle (NFC Target listening active, LCD on, radio in standby), and Peak Transaction (active NFC-DEP data exchange with simultaneous LCD redraw and ESP-NOW transmission). (I) Table 4.4 summarizes the measured current consumption and computed battery life estimates.

**Table 4.4.**
*Slave terminal current consumption profile and battery life estimates*

<!-- TODO: Use an inline ammeter (or INA219 current sensor) in series with the battery. Measure steady-state current in each mode: (1) Deep Sleep: call esp_deep_sleep_start(), read ammeter; (2) Active Idle: normal operation with no NFC tap; (3) Peak Transaction: measure peak during an active NFC+ESP-NOW burst. Compute battery life = capacity_mAh / current_mA. -->
| Operational State | Measured Current | Duration per Event | Estimated Battery Life |
|:---|:---:|:---:|:---:|
| Deep Sleep | **[TODO: measure with ammeter]** | Continuous | **[TODO: capacity_mAh / deep_sleep_current]** |
| Active Idle (NFC listening) | **[TODO: measure with ammeter]** | Continuous | **[TODO: capacity_mAh / idle_current]** |
| Peak Transaction | **[TODO: measure peak with ammeter]** | **[TODO: measure burst duration]** | N/A (transient) |

&emsp;&emsp;&emsp;<!-- TODO: Fully charge the battery, run the Slave in Active Idle with periodic simulated boarding events (e.g., 1 every 3-4 minutes to simulate ~200/shift). Log battery voltage every 5 minutes. Record the time when voltage drops to 3,300 mV. -->
&emsp;&emsp;&emsp;Under a realistic duty cycle model simulating a full minibus operating shift, with continuous Active Idle and approximately 200 Peak Transaction events per shift, the Slave terminal sustained operation for **[TODO: measure actual runtime to 3,300 mV]** hours on a single charge before reaching the 3,300 mV low-battery threshold. This **[TODO: exceeds/falls short of]** the typical 12-hour operating shift of local minibus routes in Iligan City, **[TODO: state conclusion based on actual measurement]**.
