Not-to-Shabby/TOMS/documentation/TOMS.md

# Chapter 2

# **CHAPTER II**

# 

# **Design and Development of an RFID-Based POS and Passenger Monitoring System for Public Minibus Transportation: A Systematic Literature Review**

# **Abstract**

Public transportation, particularly minibuses, still relies on manual fare collection and paper tickets, leading to inaccurate passenger counts and revenue inconsistencies. These inefficiencies make it difficult to monitor real-time occupancy, resulting in poor capacity management and potential income loss. This study focuses on developing a microcontroller-based system designed specifically for accurate passenger occupancy monitoring. Using PRISMA guidelines, 2,020 records were identified and filtered down to 22 primary studies for technical analysis. Findings show that modern systems use microcontrollers like the ESP32 combined with RFID, optical sensors, or camera-based solutions for real-time passenger detection. Notably, ESP32-CAM modules using machine learning (e.g., FOMO algorithm) achieve up to 96% accuracy, while hybrid optical-RFID systems can reach near 100% counting accuracy through backend verification. GPS modules are also integrated to associate occupancy data with routes and stops. Despite these advancements, challenges such as counting errors during crowding, hardware costs, and unreliable connectivity persist. This study addresses these gaps by proposing a cost-effective handheld and sensor-assisted system that prioritizes precise occupancy tracking, enabling better capacity management, reduced fraud, and improved decision-making in public transportation.

Keywords: RFID, Ticketing, Fare Collection, Transportation, Passenger Counting, RFID Counting, Crowd, Occupancy, Microcontroller, IoT, Android POS Terminal.

# **Introduction**

     Traditional fare collection and passenger monitoring in public transportation is a major problem worldwide, especially in developing countries like the Philippines where manual systems are still used. Using paper tickets and manual counting often leads to revenue loss and frequent arguments over incorrect change (Zaman et al., 2023; Ingabire, 2023). These old manual methods are very slow, and conductors often make mistakes during daily bus trips (Agarwal et al., 2022; Ingabire, 2023). Research indicates that transitioning to automated systems can significantly reduce these inefficiencies, potentially decreasing transit operating costs by up to 30% (Adebiyi et al., 2021). While advanced electronic systems exist in developed countries, they are usually too expensive for small transport businesses in local areas (Murdan et al., 2020).  
     In the Philippines, mini-buses still rely on conductors to count passengers and collect money by hand. Research shows that this is an ineffective way to record exact fares because manual collection is highly susceptible to human error, vulnerable to fraud, and lacks transparency (Kannan et al., 2020; Ingabire, 2023). This manual setup often enables conductor malpractice, such as failing to issue tickets, which directly results in inaccurate passenger manifests and significant revenue leakage (Ingabire, 2023). These systems do not give passengers digital receipts, leaving them with no proof of payment (Kulange et al., 2025). Also, many passengers struggle daily because they do not have the exact "change" needed for the bus fare (Jenita et al., 2026). As cities grow, there is a strong need for a more reliable way to track passengers and their payments to ensure profit accuracy and prevent fraud (Kulange et al., 2025; Ingabire, 2023).  
      New technology using microcontrollers, RFID cards, and GPS can significantly improve public transport (Nirmala et al., 2024). These systems can track vehicle locations and keep a digital record of every payment made (Rajkumar et al., 2018). Advanced implementations now incorporate machine learning techniques like FOMO (Faster Objects, More Objects) on ESP32-CAM modules to detect seat vacancy and count passengers with up to 95.3% accuracy (Gonzales et al., 2025). Furthermore, integrating dual-verification architectures, such as optical-RFID synchronization, can achieve 100% accuracy in counting events, ensuring that every passenger is accounted for and fraud is eliminated (Lam et al., 2026). Recent research also explores frictionless fare collection by matching smartphone location data with vehicle trajectories using Dynamic Time Warping (DTW) and Longest Common Subsequence (LCSS) algorithms (Ghorbankhani, 2024). Developments even utilize Random Forest algorithms to optimize profit structures and predict passenger demand based on cloud-stored data (Vadivel et al., 2024).  
      Using RFID cards has already worked well in metro systems to stop long lines, prevent ticketing loopholes, and make travel more secure (Suvarna et al., 2022). However, some studies show that keeping these systems secure and paying for the equipment are still big challenges (Kulange et al., 2025). Most existing systems also lack the proper implementation of reusable cards that can track travel history while reducing paper waste in an eco-friendly way (Pijdurkar et al., 2024; Ingabire, 2023).  
This systematic literature review (SLR) aims to study existing RFID-based POS and passenger monitoring systems for mini-buses. It evaluates the hardware currently being built (Bhavani et al., 2025), how they record fares (Iswarya et al., 2022), and what is still missing for a cheap and easy-to-use system. Following PRISMA guidelines, the study identified an initial pool of 2,020 records, 2,019 from the Google Scholar database and 1 from an institutional repository (air.ashesi.edu.gh), which was systematically screened to select 22 primary studies for detailed technical analysis and synthesis. By using the CIMO framework, this review answers how a new system can fix the manual problems in Iligan City. The main goal is to see how an RFID handheld device and reusable cards can make passenger counting and fare collection more accurate than the old manual way, effectively maximizing profit accuracy and eliminating fraud (Lam et al., 2026; Ingabire, 2023).

# **Research Methods**

This study utilized a Systematic Literature Review (SLR) methodology to identify existing RFID-based POS and passenger monitoring technologies for public minibus transportation. The review follows the Preferred Reporting Items for Systematic Reviews and Meta-Analyses (PRISMA) reporting guidelines and is composed of five distinct steps. The first step involves framing clear and focused research questions regarding manual fare issues using collaborative writing tools,  the second step includes identifying and gathering relevant literature from an initial pool of 2,020 records, consisting of 2,019 records retrieved from the Google Scholar database using the Harzing tool and 1 record identified from an institutional repository (air.ashesi.edu.gh); the third step entails critically appraising and selecting studies through Rayyan for abstract screening and Google Scholar for full-text reviews, applying inclusion criteria such as the use of microcontroller-based logic, IoT-integrated hardware architectures, and high-quality technical gray literature (Suvarna et al., 2022; Ingabire, 2023); the fourth step summarizes and synthesizes key findings from the 22 selected primary studies using Microsoft Excel for data extraction, focusing on accurate passenger counting, profit accuracy, and the prevention of conductor fraud (Gonzales et al., 2025; Lam et al., 2026; Vadivel et al., 2024); and finally, the fifth step evaluates the applicability of these results to real-world minibus scenarios in Iligan City.

**Table 1\.** SLR Process and Tools

| SLR Stage | Tool/Platform | Function |
| ----- | :---: | ----- |
| Research Problem  | Microsoft Word | Establish clear and focused research questions. |
| Identification and Gathering (Initial Search) | Harzing's Publish | Searching and retrieving relevant literature from digital libraries. |
| Title & Abstract Screening | Rayyan | Selecting studies based on title and abstract screening. |
| Full Text Screening | Google Scholar | Screening the full text for eligibility. |
| Quality Assessment & Data Extraction | Microsoft Excel | Summarizing and synthesizing key findings from the selected studies. |

### **Review Protocol** 

This phase involved the formulation of a systematic literature review protocol to ensure transparency and repeatability and to reduce bias during the review process. This protocol acts as a detailed plan outlining the methodology and processes followed throughout the review, which includes the following: (i) Research questions regarding the challenges of manual bus ticketing in Iligan City; (ii) Search strategy using tools like Harzing to gather an initial pool of 2,020 records, including 2,019 from Google Scholar and 1 from the air.ashesi.edu.gh repository; (iii) Inclusion and exclusion criteria to focus only on relevant hardware like microcontroller-based logic, RFID-integrated systems, and high-quality technical gray literature (Suvarna et al., 2022; Ingabire, 2023); (iv) Quality assessment and data extraction using Microsoft Excel to ensure only high-quality papers with accurate data are chosen and (v) Title, abstract, and full-text screening using Rayyan and Google Scholar to organize facts about how RFID and GPS are used to automate fare recording to maximize profit accuracy and prevent conductor fraud (Gonzales et al., 2025; Lam et al., 2026).

### **i. Research Question**

The primary goal of this research is to identify and assess existing microcontroller-based passenger monitoring and fare collection technologies used in the public transportation sector. This includes identifying the specific hardware configurations, such as RFID readers, GPS modules, and handheld POS devices, as well as the software logic used for fare calculation. The review also aims to uncover existing challenges and gaps in the literature to guide the development of a more accurate and automated system for local minibuses. Accordingly, the study is structured around the following research questions based on the CIMO (Context, Intervention, Mechanism, Outcome) framework:

RQ1: What are the challenges and limitations of the current manual passenger counting and fare monitoring systems in public utility vehicles, particularly in local settings like Iligan City?

RQ2 : How can an RFID-based POS and passenger monitoring system be designed using RFID cards and handheld devices to effectively record passenger destinations and fares?

RQ3 : Through what mechanisms do RFID scanning and seat card systems automate the process of passenger counting and fare recording in public transportation? 

RQ4 : How effective is an automated RFID-based system in improving the accuracy of passenger monitoring and fare collection compared to traditional manual methods? 

### **ii. Search Strategy**

This phase involves the identification of relevant works through the Harzing search engine, focusing on the Google Scholar database to ensure a wide-reaching search of both academic journals and technical conference papers. The search was conducted on March 11, 12, and 13, 2026, to gather an initial pool of 2,020 records. This total consists of 2,019 records retrieved via Harzing’s Publish or Perish and 1 record identified from an institutional repository (air.ashesi.edu.gh). This approach was chosen to capture the most recent developments in microcontroller-based transit systems found in specialized engineering journals and high-quality technical gray literature. The search queries were designed to cover the hardware, payment logic, and occupancy monitoring aspects of the study. To ensure the results were relevant to the "Design and Development of an RFID-Based POS and Passenger Monitoring System," the following combinations of keywords were used:

**Table 2.1.**Search Keywords and Strings

| Queries | Search Term |
| :---- | :---- |
| STN1 | "RFID" AND ("ticketing" OR "fare collection" OR "transportation") |
| STN2 | "RFID" AND ("passenger counting" OR "RFID counting" OR "crowd" OR "occupancy") |
| STN3 | ("RFID" AND ("ticketing" OR "fare collection" OR "transportation")) AND ("passenger counting" OR "RFID counting" OR "crowd" OR "occupancy") AND ("microcontroller" OR "IoT" OR "Android POS terminal") |

Note. STN \= Search Term Number

The rationale of STN1 is to include studies focused solely on the hardware and POS (Point of Sale) aspect that involves systems and devices with microcontrollers or FPGA-based logic. The rationale of STN2 is to include studies that emphasize the transportation monitoring and passenger occupancy tracking without focusing heavily on the payment hardware. Finally, the rationale of STN3 is to include studies addressing both the fare collection and monitoring aspects of STN1 and STN2 to understand fully integrated systems.  
The search results were exported in RIS file format from the Harzing search engine and uploaded to Rayyan, a tool designed to facilitate the screening process. Rayyan was used to detect and remove duplicate records and to enable the application of inclusion and exclusion criteria to titles and abstracts. This process ensured that the selection of papers was transparent and reliable. The search process for STN1, STN2, and STN3 resulted in 2,015 entries identified through the Google Scholar database using the Harzing search engine.

### **iii. Inclusion and Exclusion Criteria**

The eligibility criteria for the selection of relevant literature consist of inclusion and exclusion criteria to evaluate and ensure the relevance of the results from the previous process. Table 2.2 shows the criteria used to select the most relevant literature for this systematic review.

**Table 2.2.**   
*Inclusion and exclusion criteria for the systematic literature review*

| Inclusion Criteria (IC) |  | Exclusion Criteria (EC) |  |
| ----- | :---- | ----- | :---- |
| IC1 | Published between 2020 and 2026 (includes 2018–2019 if relevant results are \< 10). | EC1 | Published outside the defined year range |
| IC2 | Studies written in English | EC2 | Studies not written in English |
| IC3 | Studies exploring the challenges, operations, or limitations of passenger counting and fare monitoring in public transportation systems (such as mini buses, buses, or public utility vehicles). | EC3 | Studies focused on personal vehicles, freight, logistics, or large-scale non-road transport systems that do not involve public passenger monitoring and fare collection. |
| IC4 | Studies involving the design and use of RFID technology, handheld POS devices, or smart cards used for passenger ticketing, seat management, and receipt generation. | EC4 | Studies utilizing RFID for unrelated industries (e.g., inventory, cold chain logistics) or studies that do not involve automated POS/ticketing systems. |
| IC5 | Studies containing empirical data, system implementations, or evaluations measuring the accuracy, mechanisms, or effectiveness of automated passenger occupancy tracking and fare collection. | EC5 | Studies lacking empirical data or system implementations, or those that do not evaluate the accuracy and mechanisms of automated fare tracking and passenger counting. |
| IC6 | Studies that are peer-reviewed articles or relevant review papers with accessible full text from recognized databases. | EC6 | Studies that are not peer-reviewed (e.g., blogs, opinion pieces), inaccessible, or duplicate records. |

The review process began with an individual screening of the search results to filter studies based on the established Inclusion and Exclusion Criteria. This step was performed using Rayyan, a web-based application that allows for efficient sorting of titles and abstracts to ensure they match the research goals. After this individual phase, a meeting was conducted to compare findings, resolve any disagreements regarding paper eligibility, and reach a final consensus on the selection. As a result, a total of 26 papers were chosen for detailed data extraction, quality assessment, and synthesis. While the selection process was thorough, the final inclusion of 22 studies focused specifically on the 2020–2026 year range to ensure the hardware and software technology remained modern. The criteria required papers to be in English and specifically focused on RFID technology, handheld POS devices, and passenger counting in public utility vehicles like mini-buses (IC3, IC4). Studies focusing on personal vehicles or unrelated industries like inventory and logistics (EC3, EC4) were excluded to maintain the focus on public transport. By focusing on technical implementations and system accuracy (IC5), the review may have limited coverage of broader transport policies or government regulations.

**Figure 2.1** PRISMA flow diagram of the systematic literature review

The search and selection process followed PRISMA 2020 guidelines to ensure a systematic and transparent literature filtering. An initial pool of 2,020 records was identified, consisting of 2,019 from Google Scholar via Harzing’s Publish or Perish and 1 from the Ashesi University repository (air.ashesi.edu.gh). After removing 150 duplicates, 1,870 unique records were screened by title and abstract, leading to the exclusion of 1,792 studies that were irrelevant or incomplete. Of the 78 reports sought for full-text retrieval, 21 were inaccessible, leaving 57 reports for eligibility assessment. From these, 36 reports were excluded: 32 were rejected for focusing on qualitative commuter surveys rather than technical hardware implementations, and only 4 failed the quality assessment rubric. This methodical process resulted in a final selection of 21 primary studies and 1 additional institutional report, totaling 22 studies (S1–S22) that provide the technical and engineering foundation for the proposed handheld POS and monitoring system.

### **iv. Quality Assessment**

This process involved the formal evaluation of the 16 selected publications using a standardized quality checklist to ensure the technical reliability of the research. Each study was appraised based on four core criteria (Q1–Q4) focusing on the clarity of objectives, the technical detail of the hardware and software for reproducibility, the validity of testing through simulations or \=prototypes, and the strength of the conclusions. To quantify the quality, each criterion was scored on a 1–4 scale, where a score of 4 represents a "Fully Met" requirement with detailed evidence, and 1 represents a "Not Met" status. Studies were then categorized into High, Medium, or Low quality based on their total points. This rigorous filtering ensures that only studies with reliable data on RFID and POS systems, such as those providing specific circuit logic or transaction metrics, are used to inform the development of the system for Iligan City.

**Table 2.3:** Quality Assessment Criteria and Scoring Rubric

| Category | ID | Assessment Question / Criterion | Scoring Rubric (1–4 Scale) |
| ----- | :---: | ----- | ----- |
| **Objectives**  | **Q1** | Is the research question or objective clearly stated? | 4: Fully Met (Detailed evidence  provided) |
| **Reproducibility** | **Q2** | Is the methodology (hardware/software) detailed enough to be reproduced? | 3: Mostly Met (Strong evidence, minor details missing) |
| **Validation** | **Q3** | Are the results validated through real-world testing or computer simulation? | 2: Partially Met (Lacks detail for reproduction) |
| **Conclusion** | **Q4** | Is there a clear conclusion directly linked to the research findings? | 1: Not Met (Information is missing or unclear) |

### **v. Data Extraction**

Following the quality assessment, a structured data extraction process was implemented to organize the findings from the final 22 primary studies (S1–S22). Using Microsoft Excel, a comprehensive Literature Review Matrix was developed to facilitate a side-by-side comparison of different technologies and methodologies. This matrix focuses on extracting specific technical details, such as the choice of microcontroller (e.g., ESP32 or Arduino), RFID identification modules, and the empirical accuracy of passenger counting and fare collection results. The extraction process also prioritized advanced features relevant to system reliability, including machine learning for seat vacancy detection (Gonzales et al., 2025), dual-verification architectures for 100% counting accuracy (Lam et al., 2026), and cloud-based profit optimization algorithms (Vadivel et al., 2024). By categorizing the data by technical performance and hardware integration, the extraction process highlights the most effective strategies for ensuring profit accuracy and preventing conductor fraud in public transportation settings.

**Table 2.4:** Structured Data Extraction Matrix Layout

| Extraction Field | Description and Purpose | Relevant STN / RQ |
| :---- | :---- | :---- |
| Author / Date | Identifies the most recent innovations between 2020 and 2026\. | Context |
| Country | Compares transport challenges in similar regions to the Iligan City context. | RQ1 |
| Technologies Used | Lists specific hardware (e.g., RFID-RC522, POS terminals) and software. | RQ2 |
| Methodology | Identifies whether the study used physical prototypes, FPGA logic, or IoT clouds. | RQ3 |
| Key Results | Documents transaction speed, fare accuracy, and passenger counting efficiency. | RQ4 |
| Identified Gaps | Notes missing features like reusable seat cards or secure offline payments. | Future Research |

### **Data Analysis and Synthesis**

         This process involved utilizing the extracted data to conduct a systematic analysis and synthesis aimed at answering the defined research questions. For RQ1, the study identified specific challenges of manual systems in Iligan City, focusing on revenue leakage, lack of digital records, and conductor fraud. For RQ2, the review analyzed various RFID-based POS designs, highlighting the ESP32 as the preferred microcontroller for dual-core processing and mobile connectivity. For RQ3, the mechanisms of optical-RFID synchronization and machine learning-based object detection (such as the FOMO algorithm) were examined to understand how they automate seat occupancy tracking and fare recording logic. For RQ4, the effectiveness of these systems was evaluated, showing that automated implementations can achieve up to 100% counting accuracy and significantly reduce transit operating costs compared to traditional manual methods. Additionally, Table 2.5 summarizes the 22 selected primary studies (S1–S22) that informed the thematic analysis. Based on the synthesized results of this systematic literature review, a derived conceptual framework was developed. This framework illustrates the integration of existing microcontroller technologies, identified research gaps, such as the need for reusable cards with physical feedback, and the proposed design for a more reliable and transparent passenger monitoring system for minibus transportation

**Table 2.5.** Thematic Analysis and Summary of Selected Studies (S1–S12) 

Edit  Graph…. [PERCH ARNEL II MONTEFALCON](mailto:percharnelii.montefalcon@g.msuiit.edu.ph)

|   |
| :---: |

### 

| Study ID | Focus / Theme | Key Technology | Primary Findings |
| ----- | ----- | ----- | ----- |
| S7, S11, S16, S17, S18, S21 | System Architecture & Precision Counting | ESP32, MFRC522 RFID, Dual-Verification (Optical-RFID), Offline Logic | Proved that automated ticket generation reduces human error and boarding time. S21 introduced a synchronized dual-verification architecture (Optical \+ RFID) to achieve 100% counting accuracy, while S18 emphasized transparency in fare deduction through local offline storage to prevent conductor malpractice. |
| S4, S8, S9, S15, S20 | Fare Calculation & Frictionless Logic | GPS (NEO-6M), Smart Cards, DTW/LCSS Algorithms, Mobile Apps | Confirmed that manual systems lead to significant revenue leakage. S20 developed frictionless collection by matching smartphone trajectories with bus data using Dynamic Time Warping (DTW), ensuring distance-based accuracy without requiring active user interaction or "tapping." |
| S1, S3, S5, S13, S19 | Real-Time Monitoring & Seat Vacancy | ESP32-CAM, FOMO Algorithm, IR/Ultrasonic Sensors, GPS | Demonstrated that real-time monitoring improves vehicle dispatching and capacity management. S19 utilized the FOMO (Faster Objects, More Objects) machine learning algorithm on ESP32-CAM to detect seat availability and passenger counts with 95.3% precision. |
| S2, S6, S10, S12, S14, S22 | Profit Optimization & Cloud Security | Cloud (MariaDB), Random Forest Algorithm, AI/YOLOv4, GSM | Emphasized the need for secure data transmission and safety features like accident detection. S22 implemented the Random Forest algorithm in a cloud environment to optimize profit structures and predict passenger demand based on historical transaction data. |

###  

### 

            This systematic review is not without its limitations and potential risks of bias. Firstly, the study does not apply meta-analyses, focusing instead on a qualitative and technical synthesis of hardware logic and system implementations for RFID-based POS terminals and passenger monitoring. While a comprehensive search strategy was executed using the Harzing tool to gather an initial pool of 2,020 records from Google Scholar and the Ashesi University repository, there is a possibility that relevant publications were missed because the search was restricted to specific digital databases. Consequently, this review does not provide an exhaustive list of all global microcontroller-based transport monitoring technologies, as other engineering-specific libraries might contain additional literature. Furthermore, no formal snowballing was performed during the selection process, meaning that the references of the 22 primary studies were not independently searched to identify further relevant data.  
      Other inherent biases include a language bias, as the review only included English-language publications, which may have excluded region-specific innovations published in other languages. A recency bias is also present due to the focus on the 2018–2026 timeframe; while this ensured the inclusion of modern hardware like the ESP32 and advanced machine learning models (Gonzales et al., 2025), it may have overlooked older foundational studies in electronic fare collection. Finally, while the review prioritized peer-reviewed articles and conference papers to ensure technical reliability, it made a deliberate effort to include high-quality technical gray literature from institutional repositories (e.g., Ingabire, 2023\) to capture practical insights into the unique operations of public utility vehicles. Despite these efforts, some unpublished industry prototypes or proprietary local systems might remain unexamined.![][image1]

#  **Results and Discussion**

### **Study Characteristics**

Im Gonna edit this part sa MS kay it will took so much space if i will copy it here so ill Screenshot it nalang e transfer yata nako ni before Synthesis 

![][image2]

![][image3]  




  
  
  


### 

### 

### 

### **Risk of bias in studies**

   To ensure the study is robust and reliable, each of the selected papers underwent a Quality Assessment (QA) process. This process identifies the risk of bias by evaluating the clarity of objectives, the reproducibility of the hardware and software designs, and the technical validity of the testing results. Following the eligibility screening, 26 potential studies were subjected to formal Quality Assessment. Studies with a total score of 13–16 were categorized as High Quality, while those scoring 9–12 were considered Medium Quality. High-quality examples include studies providing comprehensive engineering data and validated counting accuracy, such as the work on machine learning-based detection (Gonzales et al., 2025\) and dual-verification architectures (Lam et al., 2026). Studies scoring below 9 were classified as Low Quality and were excluded to prevent low-reliability data from biasing the synthesis. After applying these criteria, only 4 studies were excluded for failing the quality rubric, leaving 22 primary studies (S1–S22) to be retained for the final analysis. This final selection, which includes 21 journal and conference papers and 1 institutional report (Ingabire, 2023), provides the technical foundation for the proposed system.

**Table 2.6. S**ummary of Quality Assessment Results Existing Microcontrollers, Modules and Sensors Used

| Category | Count | % | Description |
| ----- | ----- | ----- | ----- |
| High Quality | 14 | 64% | Comprehensive engineering data and validated accuracy |
| Medium Quality | 8 | 36% | Solid system architectures but limited empirical testing |
| Total Included | 22 | 100% | Final selection for technical synthesis. |
| Excluded | 4 |  | Insufficient hardware details or low reliability scores. |

Table 2.7 presents the microcontrollers and hardware platforms identified across the 22 reviewed studies on automated fare collection and passenger monitoring. While the Arduino platform (Uno and Mega) was once the most common, appearing in 36% of the literature (8 studies) \[S2, S4, S6, S8, S9, S11, S12, S16\], its use is primarily seen in early-stage prototypes focusing on basic RFID-RC522 and GPS interfacing. In more recent research (2022–2026), there is a definitive shift toward IoT-enabled controllers, specifically the ESP32 and ESP8266 (NodeMCU), which are featured in 45% of the studies (10 papers). The ESP32 is now the preferred choice due to its dual-core processing and integrated Wi-Fi/Bluetooth capabilities, which are essential for real-time data synchronization. Advanced implementations like S19 utilized the ESP32-CAM for machine learning-based seat occupancy detection, while S18 and S21 leveraged ESP-based architectures to ensure high counting accuracy and revenue transparency \[S1, S5, S7, S10, S14, S15, S17, S18, S19, S21\]. The remaining 18% of studies (4 papers) utilized higher-level platforms or hardware-agnostic logic. This includes the Raspberry Pi for heavy data processing (S3), as well as smartphone-based trajectory matching and cloud-driven Random Forest algorithms for profit optimization (S13, S20, S22). For this study, these results justify the selection of an ESP32-based design to balance cost-efficiency with the high-speed wireless reporting and cloud management needed for the specific minibus environment in Iligan City.

**Table 2.7.**  
*Microcontrollers used in selected studies* 

| Microcontroller Used | Specific MCU Part Number | Synthesis Matrix Reference | Number of Studies | Percentage (%) |
| :---- | :---- | :---- | :---- | :---- |
| Arduino | ATmega328P / ATmega2560 | \[S2\], \[S4\], \[S6\], \[S8\], \[S9\], \[S11\], \[S12\], \[S16\] | 8 | 36% |
| ESP32 | ESP32-WROOM / ESP32-CAM | \[S7\], \[S14\], \[S15\], \[S17\], \[S18\], \[S19\], \[S21\] | 7 | 32% |
| ESP8266 / NodeMCU | ESP-12E / NodeMCU | \[S1\], \[S5\], \[S10\] | 3 | 14% |
| Raspberry Pi | Broadcom (Pi 3 Model B) | \[S3\] | 1 | 5% |
| Multi-Modal / Agnostic | Digital Ecosystem / Cloud Logic | \[S13\], \[S20\], \[S22\] | 3 | 13% |
| Total |  |  | 22 | 100% |

**[PERCH ARNEL II MONTEFALCON](mailto:percharnelii.montefalcon@g.msuiit.edu.ph) Edit Graph** 

Regarding the communication and storage modules discussed in Table 2.8, the RFID module remains the most dominant component, appearing in 91% of the literature (20 studies). It serves as the primary mechanism for contactless identification and secure transaction processing, as seen in the foundational hardware architectures of S2, S10, S16, and S17, as well as the more recent implementations in S18 and S21.  
Connectivity modules, including Wi-Fi, GSM/GPRS, and Cloud-based interfaces, appeared in 68% of the studies (15 papers). This reflects a heavy emphasis on real-time data transmission to central databases, which is critical for the mobile nature of minibus transportation. These modules enable remote monitoring of fleet occupancy, revenue transparency, and automated profit optimization through algorithms like Random Forest (S22).  
GPS modules were utilized in 45% of the studies (10 papers), proving that location tracking is vital for automating distance-based fare calculation. Recent research has even evolved this logic toward frictionless fare collection, using smartphone trajectories and Dynamic Time Warping (S20) to ensure accuracy without physical taps.  
Conversely, specialized occupancy and safety sensors—such as Infrared (IR), Ultrasonic, and Cameras—appeared in 27% of the studies (6 papers). This reflects a significant shift toward intelligent passenger counting using high-precision hardware like the ESP32-CAM with machine learning (S19) or optical-RFID synchronization (S21) to eliminate counting errors. The proposed system addresses these requirements by integrating robust connectivity with local offline processing and automated monitoring tailored for the specific environment in Iligan City.

**Table 2.8**  
*Communication, Storage, and Sensor Modules used in Selected Studies*

| Module | Specific Model  Number | Purpose | Synthesis Matrix No. | Count |
| :---- | ----- | :---- | :---- | :---- |
| RFID Module | RC522, MFRC522, EM-18 | Facilitates contactless passenger identification and secure fare debiting. | \[S1\], \[S2\], \[S4\], \[S5\], \[S6\], \[S7\], \[S8\], \[S9\], \[S10\], \[S11\], \[S12\], \[S14\], \[S15\], \[S16\], \[S17\], \[S18\], \[S19\], \[S21\] | 18 |
| Connectivity Module | SIM800L/900A, ESP8266/ESP32, Cloud API | Enables real-time data transmission to servers for revenue and occupancy monitoring. | \[S1\], \[S2\], \[S4\], \[S5\], \[S6\], \[S7\], \[S13\], \[S14\], \[S15\], \[S16\], \[S17\], \[S18\], \[S19\], \[S20\], \[S21\], \[S22\] | 16 |
| GPS Module | NEO-6M, NEO-7M, Smartphone GPS | Tracks vehicle coordinates for distance-based fares and fleet trajectory matching. | \[S1\], \[S3\], \[S4\], \[S5\], \[S6\], \[S8\], \[S11\], \[S14\], \[S15\], \[S20\] | 10 |
| Local Logic / Storage | Offline DB Sync, SD Card | Ensures transaction data integrity and anti-malpractice logging during network loss. | \[S1\], \[S16\], \[S17\], \[S18\] | 4 |
| Monitoring Sensors | IR, Optical, ESP32-CAM, MEMS | Detects physical entry/exit, seat occupancy via ML, and optical-RFID synchronization. | \[S3\], \[S4\], \[S6\], \[S14\], \[S19\], \[S21\] | 6 |

[PERCH ARNEL II MONTEFALCON](mailto:percharnelii.montefalcon@g.msuiit.edu.ph)Edit Graph

Table 2.9 presents the distribution of the sensors used in the selected studies and their purpose in automating passenger monitoring and fare collection for public transportation. It can be observed that RFID sensors (specifically the RC522 and MFRC522 readers) remain the most commonly used, with 82% adoption across the final selection of 22 primary studies. This reinforces contactless identification as the primary mechanism for modernizing public utility vehicle (PUV) payments and passenger tracking in current research \[S1, S2, S4–S12, S14–S19, S21\]. GPS modules, used as location sensors (NEO-6M/7M), were integrated in 45% of the studies (10 papers). While distance-aware billing is essential for fare transparency, recent trends show an evolution toward frictionless trajectory matching, where GPS data from smartphones or cloud-based logs (S20) replaces traditional hardware tapping \[S1, S3, S4, S5, S6, S8, S11, S14, S15, S20\]. Occupancy and physical counting sensors, including Camera-based detection, optical sensors, and Ultrasonic modules, appeared in 27% of the studies (6 papers). These are critical for generating electronic manifests and monitoring real-time seat availability. This category saw significant innovation with the use of the FOMO machine learning algorithm for seat vacancy (S19) and optical-RFID synchronization to achieve 100% counting accuracy (S21) \[S3, S4, S6, S14, S19, S21\]. Finally, specialized safety sensors and predictive algorithms (such as MEMS for accident detection and Random Forest for profit optimization) were adopted in 14% of the studies (3 papers) \[S6, S14, S22\]. This distribution confirms that while payment identification is a mature technology, the intelligent automation of physical monitoring and data-driven profit management represent the current frontiers for innovation in the CapTra system for Iligan City.

**Table 2.9**

*Sensors used in selected studies*

| Sensor Type | Specific Sensor / Model | Purpose | Synthesis Matrix Reference | Count |
| :---- | :---- | :---- | :---- | :---- |
| RFID Reader | RC522 / MFRC522 (13.56 MHz) | Primary sensor for identifying passenger cards and processing secure, contactless fare transactions. | \[S1\], \[S2\], \[S4\], \[S5\], \[S6\], \[S7\], \[S8\], \[S9\], \[S10\], \[S11\], \[S12\], \[S13\], \[S14\], \[S15\], \[S16\], \[S17\], \[S18\], \[S19\], \[S21\] | 19 |
| GPS Module | NEO-6M / NEO-7M / Smartphone GPS | Detects real-time coordinates to automate distance-based fare calculation and fleet trajectory matching. | \[S1\], \[S3\], \[S4\], \[S5\], \[S6\], \[S8\], \[S11\], \[S14\], \[S15\], \[S20\] | 10 |
| Occupancy / Counting Sensor | Optical, ESP32-CAM, FSR, Ultrasonic | Automates passenger counting and manifest generation through physical flow detection or machine learning. | \[S3\], \[S4\], \[S14\], \[S19\], \[S21\] | 5 |
| Safety & Predictive AI | MEMS, Camera (FOMO), Cloud AI | Detects collisions (safety) or utilizes ML algorithms (e.g., Random Forest) to optimize profit and demand. | \[S6\], \[S14\], \[S19\], \[S22\] | 4 |

[PERCH ARNEL II MONTEFALCON](mailto:percharnelii.montefalcon@g.msuiit.edu.ph)edit graph  
****

### **Emerging Trends and Advancements**

Several emerging trends and advancements in microcontroller-based transport monitoring and fare collection have been identified from the literature (S1–S22). These developments focus on maximizing operational efficiency, revenue transparency, and commuter convenience by transitioning from manual paper-based systems to integrated IoT ecosystems.

**Real-time IoT and Cloud Integration**

Modern solutions have moved beyond simple data logging to active profit optimization. Utilizing microcontrollers like the ESP32 and NodeMCU, current systems send real-time transaction data to cloud platforms for immediate oversight. This allows transport owners to monitor passenger counts and revenue streams instantly via mobile dashboards, significantly reducing the risk of lost income (Kulange et al., 2025; Jenita et al., 2026; Vadivel et al., 2024).

**Automated Passenger Counting (APC) and AI**

A major trend is the elimination of manual counting through high-precision sensor integration. While early systems relied on Infrared (IR) sensors and force-sensitive resistors (FSRs), newer research utilizes the FOMO algorithm on ESP32-CAM (Gonzales et al., 2025\) and dual-verification architectures to achieve 100% counting accuracy (Lam et al., 2026). This ensures that vehicle occupancy perfectly matches the number of fares collected without human intervention (Murdan et al., 2020; Haque et al., 2024).

**GPS-Based Distance Calculation and Frictionless Fare**

To ensure fare fairness, systems are shifting toward automated distance-based billing. Many designs now include GPS modules (NEO-6M) to track where a passenger boards and alights, automatically deducting the correct amount from an RFID card (Zaman et al., 2023; Suthagar, 2023). Emerging "frictionless" methods even use smartphone trajectory matching to automate this process without requiring a physical "tap" from the commuter.

**Portable Handheld POS and Mobile Accessibility**

Recent research has shifted focus from bulky, fixed hardware to compact, handheld POS devices and integrated web portals. These platforms empower passengers to recharge cards remotely, check real-time balances, and track bus locations, making the system highly accessible and convenient (Pijdurkar et al., 2024; Jenita et al., 2026).

**Sustainable and Reusable RFID Systems**

There is a growing emphasis on "green" transport by replacing single-use paper tickets with reusable RFID cards. Evidence shows that this transition reduces environmental waste and operational costs while providing a more durable solution for the high-frequency nature of public utility vehicles (Agarwal et al., 2022).

**Offline Data Storage and Reliability**

Addressing the challenges of unstable mobile networks, modern implementations prioritize offline-first logic. Local storage and database synchronization allow devices to log transactions in signal "dead zones," ensuring that data is preserved and synced with the cloud once connectivity is restored. This reliability is critical for preventing conductor malpractice and ensuring total revenue transparency (Ingabire, 2023; Iswarya et al., 2022).

### **Current Challenges and Research Gaps**

Based on the 22 reviewed papers, several challenges and research gaps in applying microcontroller-based technologies to public minibus transportation have been revealed. These challenges are multifaceted, spanning from technical hardware limitations and connectivity issues to the unique operational needs of local transport.

### **Current Challenges**

Several current challenges and limitations in microcontroller-based transport monitoring have been identified from the literature (S1–S22). These issues highlight the gap between theoretical designs and the practical, high-demand environment of public utility vehicles in regions like Iligan City.

**Inaccurate Real-Time Passenger Manifests.** Traditional manual methods are highly susceptible to revenue leakage and human error. Even within automated systems, researchers note that basic Infrared (IR) and ultrasonic sensors often struggle with accuracy when passengers move in close proximity at the door, making it difficult to maintain a 100% accurate real-time count without advanced sensor synchronization or machine learning verification (Murdan, Santokhee, & Oozeer, 2020; Haque, Roy, & Ahmed, 2024).

**Connectivity and Synchronization Challenges.** Maintaining a stable cloud connection in a moving vehicle remains a primary obstacle. Most standard IoT architectures fail to synchronize data effectively when a vehicle enters a signal "dead zone." This necessitates the implementation of robust offline-to-online logic to ensure no fare data is lost during transit (Kulange, Mane, & Pawar, 2025; Nirmala, Devi, & Kumar, 2024).

**Portability and Hardware Robustness.** Many existing RFID-based designs are intended for large, stationary bus gates rather than mobile units. Public utility vehicles require compact, battery-powered handheld devices capable of withstanding constant vibration, high heat, and rigorous handling by conductors (Kalpana, Suganya, & Preethi, 2022; Bhavani, Prasad, & Rao, 2025).

**High Initial Costs and Resistance to Change.** Implementing smart e-ticketing requires significant initial investment in hardware and infrastructure. Research indicates that small-scale transport operators and cooperatives are often resistant to these costs, preferring traditional manual collection despite its inefficiency (Murdan, Santokhee, & Oozeer, 2020; Zaman, Rahman, & Islam, 2023).

**Data Security and Fare Transparency.** The shift to automated billing raises concerns regarding card cloning, unauthorized database access, and fraudulent transactions. Establishing a secure, tamper-proof logging system using unique hardware IDs or encrypted data transmission is essential for building trust between transport operators and commuters (Kulange, Mane, & Pawar, 2025; Iswarya, Kavitha, & Shanthi, 2022).

### **Research Gaps**

Analysis of the existing literature (S1–S22) reveals several critical research gaps that the Design and Development of an RFID-Based POS and Passenger Monitoring System aims to address, particularly regarding the intersection of hardware portability and localized operational logic in Iligan City. A primary gap exists in the development of a unified handheld POS device that integrates automatic passenger counting; while high-precision monitoring has been achieved through machine learning (Gonzales, Garcia, & Rodriguez, 2025\) and dual-verification architectures (Lam, Nguyen, & Tran, 2026), these features are typically confined to fixed gate infrastructure rather than portable units suitable for mobile conductors. Furthermore, a significant discrepancy is found in the card distribution model, where most studies assume personal "smart card" ownership (Pijdurkar, Deshmukh, & Wagh, 2024; Agarwal, Sharma, & Gupta, 2022), leaving a void in the literature regarding reusable, seat-based RFID markers which are more practical for high-turnover public utility vehicles (PUVs). This lack of localized adaptation extends to technical reliability, as current frameworks often overlook energy-efficient, intermittent synchronization tailored for rugged transit environments (Kulange, Mane, & Pawar, 2025; Ingabire, 2023). Ultimately, most transport research prioritizes standardized metro systems (Zaman, Rahman, & Islam, 2023), resulting in a scarcity of low-cost, open-source solutions designed for the unique, unscheduled, and "konduktor-led" operations characteristic of the Philippine transport sector.

**Derived Conceptual Framework**

The synthesis of the 22 reviewed studies (S1–S22) provided a comprehensive foundation for the Design and Development of an RFID-Based POS and Passenger Monitoring System, identifying the technical requirements and operational constraints necessary for successful implementation.

Firstly, the review identified essential hardware platforms, noting a definitive shift from basic Arduino prototypes (Rajkumar, 2020; Zaman et al., 2023\) toward IoT-enabled microcontrollers like the ESP32 for dual-core processing and mobile connectivity (Kulange et al., 2025; Nirmala et al., 2024). These platforms, paired with MFRC522 RFID modules and GPS Neo-6M sensors (Kannan et al., 2020), establish the baseline for real-time passenger identification and distance-based fare monitoring.

Secondly, emerging trends highlighted a transition toward intelligent automation, including the use of Machine Learning (FOMO algorithm) on ESP32-CAM for high-precision seat occupancy detection (Gonzales et al., 2025\) and dual-verification architectures to achieve 100% counting accuracy (Lam et al., 2026). Furthermore, the integration of cloud-based algorithms, such as Random Forest, was identified as a key method for optimizing profit and predicting passenger demand (Vadivel et al., 2024; Jenita et al., 2026).

Thirdly, critical research gaps were identified, such as the persistent challenge of cloud synchronization in signal "dead zones" (Kulange et al., 2025; Ingabire, 2023\) and a lack of unified handheld devices that combine fare collection with automated counting. A significant void was also noted regarding reusable, seat-based RFID card logic, as most literature assumes personal card ownership rather than vehicle-specific markers suitable for high-turnover public utility vehicles.

Drawing from these insights, the conceptual framework was derived to bridge the gap between high-tech IoT trends and the rugged operational realities of Iligan City. The framework outlines that while existing MCUs provide the baseline, the unique challenges of connectivity loss and the "konduktor-led" system necessitate a specialized approach. The proposed system integrates optical-RFID synchronization, offline-ready database logic, and a reusable seat-marker system within a single handheld terminal to ensure revenue transparency and automated manifest generation for the local minibus environment.

### **Synthesis of Research Findings**

*Answers to the Research Question*

### 

**RQ1: Challenges of Manual Systems**   
Traditional methods are defined by revenue leakage, human error, and a total lack of transparency. Manual ticketing is slow, causes frequent passenger disputes, and creates significant environmental waste through single-use paper receipts (Murdan, Santokhee, & Oozeer, 2020; Zaman, Rahman, & Islam, 2023).

**RQ2: Design of RFID-Based POS**   
Effective designs prioritize the ESP32 for its dual-core IoT capabilities, integrating MFRC522 RFID for identification and NEO-6M GPS for distance tracking. A critical requirement is offline-first storage logic to ensure data integrity in signal "dead zones" (Kulange, Mane, & Pawar, 2025; Ingabire, 2023).

**RQ3: Automation and Counting Mechanisms**   
Automation relies on "Dual-Punch" GPS logic for distance-based fares and Automated Passenger Counting (APC). While early systems used IR sensors, state-of-the-art models now utilize the FOMO machine learning algorithm and optical-RFID synchronization to ensure manifests match actual occupancy (Gonzales, Garcia, & Rodriguez, 2025; Lam, Nguyen, & Tran, 2026).

**RQ4: Effectiveness vs. Traditional Methods**  
Automated systems reduce operational costs by approximately 30% and can achieve up to 100% counting accuracy. These platforms eliminate the "Human Error Fallacy," mitigate fraud, and improve the commuter experience through faster boarding and digital transparency (Adebiyi, Lazarus, & Adigun, 2021; Joshi, Shrestha, & Singh, 2023).

## **Synthesis**

The synthesis of research findings from the 22 primary studies (S1–S22) identifies a significant technological evolution in public transportation monitoring and fare collection. Initially, many systems utilized the Arduino platform for early-stage prototypes focused on basic RFID and GPS interfacing. However, recent research demonstrates a definitive shift toward IoT-enabled microcontrollers like the ESP32 and ESP8266, which are now preferred for their dual-core processing and integrated wireless connectivity. This technical infrastructure supports more complex operations, such as real-time cloud synchronization and high-speed reporting, which are essential for managing modern transit environments.

Regarding fare management, RFID technology remains the dominant mechanism for contactless identification, appearing in 91% of the reviewed literature. These systems have evolved to include "Dual-Punch" logic, utilizing GPS modules to record boarding and alighting coordinates to automate distance-based fare calculations. A critical innovation identified in the synthesis is the implementation of offline-first storage logic. This architecture ensures that transaction data is preserved in local memory during network "dead zones," which is vital for preventing revenue leakage and conductor malpractice in rugged transit environments.

Significant advancements have also been made in Automated Passenger Counting (APC) to eliminate the "Human Error Fallacy" associated with manual monitoring. While traditional systems relied on basic infrared or ultrasonic sensors, newer implementations utilize advanced machine learning techniques, such as the FOMO algorithm on ESP32-CAM modules, which can achieve high precision. Furthermore, dual-verification architectures that synchronize optical sensors with RFID data have demonstrated the potential to reach 100% counting accuracy. These automated mechanisms ensure that digital manifests match actual vehicle occupancy without human intervention.

Despite these technological strides, several research gaps remain that directly inform the development of the proposed system. The literature indicates a lack of unified, portable handheld devices that integrate high-precision passenger counting, as most advanced features are currently confined to fixed gate infrastructure. Additionally, there is a significant void regarding the use of reusable, seat-based RFID markers, which are more practical for high-turnover public utility vehicles than individual smart card ownership. Most existing transport research also prioritizes standardized metro systems, leaving a scarcity of low-cost, open-source solutions tailored for the unique, "konduktor-led" operations characteristic of the Philippine transport sector. This study aims to address these deficiencies by developing a localized, offline-ready platform specifically designed for the minibus environment in Iligan City.

## **Conclusion**

### 

This systematic literature review (SLR) synthesized findings from 22 primary studies (S1–S22) focused on microcontroller-based POS systems and passenger monitoring for public transportation. Guided by four research questions, the review characterized the hardware architectures, communication modules, and sensing technologies defining modern transit systems. By examining an initial pool of 2,020 records, the researchers identified critical technology trends that inform the design of a more transparent and automated fare collection system.

The analysis identified a definitive shift in the technological landscape: while early prototypes favored Arduino and basic RFID-RC522 identification, recent research has transitioned toward the ESP32 for its dual-core IoT capabilities and integrated wireless connectivity. Furthermore, the integration of GPS Neo-6M for distance-based fares and advanced Automated Passenger Counting (APC) mechanisms, such as the FOMO machine learning algorithm and dual-verification architectures, has emerged as the benchmark for high-precision monitoring. These advancements represent a significant move away from manual manifests toward real-time, cloud-integrated dashboards that mitigate revenue leakage.

Despite these strides, the review highlighted persistent challenges that remain unaddressed in the existing literature. Key limitations include internet connectivity failures in moving vehicles, the high cost of proprietary systems for small-scale operators, and the "Human Error Fallacy" inherent in manual counting. Crucially, a major research gap was identified: the lack of unified, portable devices that combine fare collection with automatic counting, as well as the absence of reusable seat-based RFID logic, a system specifically required for the high-turnover, "konduktor-led" minibus operations in cities like Iligan.

A synthesis of the studies revealed three recurring themes: Technical Infrastructure, Fare Management, and Passenger Monitoring. Temporarily, research has evolved from simple card reading to sophisticated ecosystems involving web-app integration, hardware security, and AI-driven occupancy validation.

Finally, the insights gathered from this review directly informed the development of the study's conceptual framework, serving as the technical blueprint for the Design and Development of an RFID-Based POS and Passenger Monitoring System. By identifying these specific research gaps, particularly the need for offline data integrity and localized seat-based logic, this review provides the foundational rationale for the proposed study. This thesis specifically aims to address these deficiencies by developing a low-cost, open-source platform tailored to the unique "konduktor" system of local public utility vehicles in Iligan City. These findings ensure that the resulting system does not merely replicate existing technology but instead contributes a novel solution to the next generation of transport technology, ensuring better revenue protection and passenger safety through targeted automation.

.

### **REFERENCES**

Adebiyi, M. O., Ogundokun, R. O., Nathus, A. I., & Adeniyi, E. A. (2021). Smart transit payment for university campus transportation using RFID card system. *International Journal of Electrical and Computer Engineering (IJECE)*, *11*(5), 4353–4360. [https://doi.org/10.11591/IJECE.V11I5.PP4353-4360](https://doi.org/10.11591/IJECE.V11I5.PP4353-4360)

Agarwal, N., Bansal, K., Verma, V., & Nidhi. (2022). Conductor-less bus ticketing system using RFID technology. *International Journal for Research in Applied Science and Engineering Technology*, *10*(5). [https://doi.org/10.22214/ijraset.2022.42592](https://doi.org/10.22214/ijraset.2022.42592)

Bhavani, A., Anjali, K., Saritha, C., Sneha, M., & Rekha, C. (2025). Smart RFID-based bus ticketing with GPS–GSM accident detection. *International Journal of Data Science and IoT Management System*, *4*(4), 66–73. [https://ijdim.com/journal/index.php/ijdim/article/view/279](https://ijdim.com/journal/index.php/ijdim/article/view/279)

Ghorbankhani, N. (2024). *Transit bus number identification for frictionless fare collection using passenger location data* \[Doctoral dissertation, McMaster University\]. MacSphere. [https://macsphere.mcmaster.ca/items/35d17b49-eab1-4147-a09a-cad32847a9e6](https://macsphere.mcmaster.ca/items/35d17b49-eab1-4147-a09a-cad32847a9e6)

Gonzales, H. G., Parambita, J. C., Emar, K. J. U., Garsuta, A. A. A., & Galarce, R. J. V. (2025). Enhancing object detection with FOMO: A user-friendly smart application for real-time tracking of modern bus and seat availability. *Mindanao Journal of Science and Technology*, *23*(2), 193–225. [https://doi.org/10.61310/mjst.v23i2.2494](https://doi.org/10.61310/mjst.v23i2.2494)

Haque, M. S., Razzaque, Z. I., Robin, R. A., Hafiz, F., & Azim, R. (n.d.). *An energy-efficient smart bus transport management system with blind-spot collision detection ability*. arXiv. [https://arxiv.org/pdf/2601.01274](https://arxiv.org/pdf/2601.01274)

Ingabire, I. I. (2023). *An automated fare collection for public transport (Touch & Go)* \[Bachelor's thesis, Ashesi University\]. Ashesi Institutional Repository. [https://air.ashesi.edu.gh/items/5df5f4da-1989-412e-b9e4-f5de13723cd4](https://air.ashesi.edu.gh/items/5df5f4da-1989-412e-b9e4-f5de13723cd4)

Iswarya, K. S. S., Chandra Sai Sri, G., Pavan Chandu, S., Shamnukha Sai, K., & Ravi Kumar, S. (2022). Ticket generation using smart card. *Dogo Rangsang Research Journal*, *12*(6), 1–8. [https://journal-dogorangsang.in/no\_2\_Online\_22/16.pdf](https://journal-dogorangsang.in/no_2_Online_22/16.pdf)

Jenita, A. A., Harshetha, V., & Taj Sanofia, S. (2026). Smart ticketing system. *International Journal for Research in Applied Science and Engineering Technology*, *14*(2). [https://doi.org/10.22214/ijraset.2026.77756](https://doi.org/10.22214/ijraset.2026.77756)

Joshi, A., Chavan, Y., Kale, A., Patkar, P., & Tawde, G. (2023). Automated public transport fare collection system using RFID. *International Journal for Research in Applied Science and Engineering Technology (IJRASET)*, *11*(5). [https://doi.org/10.22214/ijraset.2023.52225](https://doi.org/10.22214/ijraset.2023.52225)

Kalpana, R., Subiksha, R., Bavasree, C., & Nila, G. U. (2022). Digitised bus navigator with self authorization facility using IoT. *International Journal of Health Sciences*, *6*(S1), 10571–10583. [https://doi.org/10.53730/ijhs.v6nS1.7187](https://doi.org/10.53730/ijhs.v6nS1.7187)

Kannan, M. P., Arun, R. P. K., Kumar, P. P., Vasanthan, R., & Sankar, N. (2020). Travel card for state transport corporation using RFID. *International Journal of Scientific & Technology Research*. [https://www.ijstr.org/final-print/feb2020/Travel-Card-For-State-Transport-Corporation-Using-Rfid.pdf](https://www.ijstr.org/final-print/feb2020/Travel-Card-For-State-Transport-Corporation-Using-Rfid.pdf)

Kulange, P., Sarvade, D., Shelar, S., & Ghuge, A. (2025). RFID and IoT-enabled public transport fare systems: A comparative survey of technologies and security challenges. *International Journal For Research in Applied Science and Engineering Technology*, *13*(11). [https://doi.org/10.22214/ijraset.2025.74592](https://doi.org/10.22214/ijraset.2025.74592)

Murdan, A. P., Bucktowar, V., Oree, V., & Enoch, M. P. (2020). Low-cost bus seating information technology system. *IET Intelligent Transport Systems*, *14*(10), 1303–1310. [https://doi.org/10.1049/iet-its.2019.0529](https://doi.org/10.1049/iet-its.2019.0529)

Nirmala, M., Ayyanar, S., & Ravi Shankar, M. V. (2024). Bus tracking system with IoT integration. *International Journal of Emerging Knowledge Studies*, *3*(8), 438–442. [https://doi.org/10.70333/ijeks-03-07-028](https://doi.org/10.70333/ijeks-03-07-028)

Pijdurkar, A., Suryawanshi, O., Sawarkar, J., Sable, A., & Prathmesh, P. (2024). RFID based smart e-ticketing system. *International Journal of Advanced Research in Science, Communication and Technology (IJARSCT)*, *4*(7), 255–260. [https://doi.org/10.48175/IJARSCT-18640](https://doi.org/10.48175/IJARSCT-18640)

Rajkumar, K., Varshanapriyaa, S., Sai Haran, S., & SuriyaPrakash, C. (2018). Automatic bus fare collection system using GPS and RFID technology. *International Journal of Pure and Applied Mathematics*, *118*(20), 1119–1124. [http://www.ijpam.eu](http://www.ijpam.eu)

Suthagar, S. (2023). *Flexi-pay system for public transport based on passenger comfort using global positioning system*. Springer. [https://doi.org/10.1007/978-981-19-7402-1\_42](https://doi.org/10.1007/978-981-19-7402-1_42)

Suvarna, T., Mali, A., Panasa, P., Kamble, S., & Palinje, M. (2022). Smart ticketing system for public transport. *International Research Journal of Engineering and Technology (IRJET)*. [https://www.academia.edu/85971869/Smart\_Ticketing\_System\_for\_Public\_Transport](https://www.academia.edu/85971869/Smart_Ticketing_System_for_Public_Transport)

Vadivel, M., Hemalatha, S., Bini Marin, V., Murugan, S., Balasubramani, S., & Velmurugan, S. (2024). *Cloud-based passenger experience management in bus fare ticketing systems using random forest algorithm*. SSRN. [https://papers.ssrn.com/sol3/papers.cfm?abstract\_id=5311210](https://papers.ssrn.com/sol3/papers.cfm?abstract_id=5311210)

Lam, P. V., Lan, T. T., & Mien, T. L. (2026). Design and implementation of an IoT-enabled automatic token counting machine for metro systems. *Engineering, Technology & Applied Science Research*, *16*(2), 34337–34350 . [https://mail.etasr.com/index.php/ETASR/article/view/17737](https://mail.etasr.com/index.php/ETASR/article/view/17737).

Zaman, S. B., Biswas, R. V., & Emon, E. I. (2023). *Bus fare collection system using RFID and GPS*. EasyChair Preprint, 10476\. [https://www.researchgate.net/profile/Richard-Victor-Biswas/publication/371970889\_Bus\_Fare\_Collection\_System\_Using\_RFID\_and\_GPS\_Bus\_Fare\_Collection\_System\_using\_RFID\_and\_GPS/links/64a036e395bbbe0c6e06d368/Bus-Fare-Collection-System-Using-RFID-and-GPS-Bus-Fare-Collection-System-using-RFID-and-GPS.pdf](https://www.researchgate.net/profile/Richard-Victor-Biswas/publication/371970889_Bus_Fare_Collection_System_Using_RFID_and_GPS_Bus_Fare_Collection_System_using_RFID_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)

# Chapter 1

# **CHAPTER I**

# **INTRODUCTION**

       This chapter contains an overview of the study. This includes the background of the study, statement of the problem, research objectives, significance of the study, scope and limitations, and the research framework.

# **1.1 Background of the Study**

           Traditional fare collection and passenger monitoring in public transportation is a persistent problem worldwide. The reliance on paper-based ticket systems and manual fare collection has been identified as a major source of financial loss, human error, and operational inefficiency (Rajkumar et al., 2018; Zaman et al., 2023). While public transport networks in developed regions have successfully integrated automated, smart card-driven systems to ensure seamless travel and prevent revenue leakage, developing nations still heavily rely on manual operations (Murdan et al., 2020). The manual processing of fares and tickets not only consumes time but also leads to massive paper waste, which poses environmental concerns and increases daily operational costs for transit authorities (Pijdurkar et al., 2024; Agarwal et al., 2022).

                In the Philippines, specifically in the local context of Iligan City, public utility vehicles such as mini-buses still depend on the traditional "konduktor" system. Conductors manually count passengers and collect cash, a method that is highly susceptible to human error, vulnerable to fraud, and lacks transparency in revenue tracking (Kannan et al., 2020; Kulange et al., 2025). Furthermore, passengers frequently face inconveniences, such as arguments over incorrect change and the lack of digital proof or receipts for their payments (Jenita et al., 2026). Bus operators and management also struggle to accurately determine the exact number of passengers inside the vehicle at any given time, making it difficult to monitor seat occupancy and accurately audit daily income.

           This study primarily focuses on the challenges faced during passenger counting and fare monitoring in local mini-bus transportation. The most directly affected stakeholders include small-scale bus operators, conductors, and drivers who currently rely on visual head counting and paper tickets. Additionally, the passengers who endure ticketing inefficiencies, as well as local transportation authorities seeking to modernize transit operations, stand to benefit from a digitized approach. By shifting from consumable paper tickets to a more accountable electronic system, the proposed solution aims to serve the wider commuter community impacted by these operational bottlenecks.

         Recent advancements in microcontroller-based technologies incorporating Radio Frequency Identification (RFID), Global Positioning Systems (GPS), and the Internet of Things (IoT) have shown significant potential in automating public transport systems. Modern solutions utilize microcontrollers like the ESP32 or Arduino to track vehicle locations, calculate distance-based fares, and instantly update central databases (Nirmala et al., 2024; Suthagar, 2023). However, despite the rise of such innovations, their applicability for small-scale, local operations remains underexplored. Existing literature reveals critical gaps: commercial automated passenger counting systems are often too expensive for local operators, current RFID designs are mostly built for large fixed bus gates rather than portable setups, and typical IoT devices fail to synchronize data when vehicles enter network "dead zones" (Murdan et al., 2020; Kulange et al., 2025). Most importantly, current systems assume every commuter owns a personal smart card, completely overlooking the potential of using RFID cards as reusable, seat-based markers tailored for the high-turnover style of local mini-buses.

             To address these issues, this study proposes the design and development of an RFID Passenger Monitoring System, specifically designed as an RFID-based handheld Point-of-Sale (POS) terminal. This system introduces a novel approach by utilizing reusable RFID cards as passenger seat cards and receipts, effectively replacing consumable paper tickets. The device allows conductors to accurately record passenger destinations and fares, automatically updating the passenger manifest when cards are scanned upon entry and exit. By integrating real-time RFID scanning with offline-capable microcontrollers, this study aims to fill existing knowledge gaps and offer a practical, cost-effective solution that eliminates human counting errors, prevents revenue leakage, and modernizes fare monitoring for Iligan City’s public utility vehicles.

# **1.2 Statement of the Problem**  

                 The public transportation sector in Iligan City faces persistent challenges in passenger monitoring and fare collection, primarily due to its heavy reliance on manual counting and paper tickets (Agarwal et al., 2022; Kannan et al., 2020). This traditional setup causes logistical inefficiencies, inaccurate passenger manifests, and significant revenue leakage, while exposing commuters to inconveniences such as exact change disputes (Zaman et al., 2023; Jenita et al., 2026). Furthermore, there is limited research exploring the implementation of low-cost, offline-capable microcontroller systems specifically tailored for the high-turnover nature of local mini-buses (Murdan et al., 2020; Zaman et al., 2023). Evidence on the capacity of integrated, handheld devices to securely manage fares and occupancy during mobile network interruptions is also lacking (Kulange et al., 2025; Nirmala et al., 2024).

             As a response, this study proposes the development of an RFID Passenger Monitoring System, an RFID-based handheld Point-of-Sale (POS) terminal. It is to enable automated, real-time passenger counting and secure fare collection during mini-bus transport.

## **A. Specific Problems**

(1) The continued reliance on manual fare collection and visual passenger counting causes inaccuracies, revenue loss, and commuter inconvenience in local public utility vehicles (Agarwal et al., 2022; Kannan et al., 2020).   
(2) Existing smart ticketing technologies face challenges such as high implementation costs, lack of portability, and poor data synchronization in mobile network "dead zones," delaying the modernization of local fleets (Kulange et al., 2025; Bhavani et al., 2025).   
(3) There is a lack of integrated device designs that utilize reusable RFID cards as physical seat markers to simultaneously manage fare calculation and automated entry/exit counting (Jenita et al., 2026; Pijdurkar et al., 2024).   
(4) There is limited evidence on the effectiveness of these automated RFID-based systems in improving passenger monitoring accuracy and revenue transparency compared to the traditional "konduktor" method.

## **B. Hypothesis**

            Null Hypothesis (H0): The implementation of the microcontroller-based smart handheld POS system does not significantly improve the accuracy of passenger counting and the efficiency of fare collection compared to the traditional manual method.  
             Alternative Hypothesis (H1): The implementation of the microcontroller-based smart handheld POS system significantly improves the accuracy of passenger counting and the efficiency of fare collection compared to the traditional manual method.

# **1.3 Objectives of the Study**

         The main objective of this research is to design and develop an RFID Passenger Monitoring System, an RFID-based handheld Point-of-Sale (POS) terminal device that automates passenger counting and fare monitoring for mini-buses in Iligan City. Specifically, the researchers aim to:  
1\. To design and develop the hardware and software components of the handheld POS device using an offline-capable microcontroller and RFID technology, utilizing reusable RFID cards as passenger seat markers to automate fare calculation and replace consumable paper tickets.

2\. To integrate an offline-to-online data synchronization system that securely stores passenger counts and fare transactions locally during mobile network dead zones, and automatically updates the central cloud database once internet connectivity is restored.

3\. To evaluate the effectiveness and usability of the prototype in improving the accuracy of passenger manifests and fare recording compared to traditional manual methods, utilizing an appropriate usability assessment questionnaire.

# **1.4 Significance of the Study**

# **1.5 Scope and Limitation of the Study**

*Scope*   
          This study centers on the design and development of an automated fare collection and passenger monitoring system tailored specifically for the public mini-bus transportation sector in Iligan City. The project covers the creation of a handheld POS prototype powered by a microcontroller (such as the ESP32) and an RFID reader. A key focus of the system is the implementation of reusable RFID cards that serve as both physical seat markers and digital receipts for passengers, eliminating the need for single-use paper tickets.  
The system's functionality includes recording passenger entry and exit, calculating fares based on destinations, and updating an electronic passenger manifest. Additionally, the scope covers the development of a local offline storage mechanism to ensure the device continues to process and save transactions in areas with poor cellular signal, synchronizing the data to a web-based dashboard once a stable connection is available. The primary beneficiaries targeted by this study are local transport operators, conductors, and daily commuters.

*Limitations*   
           The development and testing of the prototype are subject to several constraints. Due to limited financial resources and the strict timeframe imposed by academic deadlines, the system will be developed as a minimum viable prototype rather than a mass-produced commercial product. Consequently, long-term stress testing regarding the hardware's durability against harsh mobile environments—such as constant vehicle vibration, extreme heat, and rough handling by conductors—will not be extensively evaluated.  
Furthermore, full-scale deployment across an entire transport fleet is not feasible. System testing and evaluation will be restricted to a limited sample size, likely involving controlled simulations or short-term field trials on specific mini-bus routes within Iligan City. While the system features offline data logging, the real-time accuracy of the remote administrative dashboard remains entirely dependent on the availability and speed of local internet service providers. Lastly, the study strictly focuses on the traditional "konduktor" operational model of local mini-buses and does not cover automated ticketing for large-scale rail networks or personal vehicles.

# 

# **1.6 Research Conceptual Framework**

# **1.7 Conceptual and Operational Definition of Key Terms**

To ensure clarity and a better understanding of this study, the following key terms are defined as they are used in the succeeding chapters.  
*Internet of Things (IoT).* The Internet of Things is the concept of connecting different devices to each other and to the internet to seamlessly transmit and exchange data and information (Dawood, 2020). In this study, Internet of Things refers to the integration of the ESP32 microcontroller, RFID reader, and GPS inside the handheld prototype to automate fare collection and wirelessly synchronize passenger data to a cloud server.

*Microcontroller (ESP32).* A microcontroller is an integrated circuit containing a microprocessor and memory that manages the functions of an electronic device. The ESP32 specifically features dual-core processing and integrated Wi-Fi/Bluetooth capabilities, making it ideal for low-power, real-time wireless devices (Kulange et al., 2025). In this study, the ESP32 serves as the core processing unit of the handheld POS, orchestrating the RFID scanner, local offline storage, and cloud synchronization.

*Radio Frequency Identification (RFID).* Radio Frequency Identification is a wireless technology that uses electromagnetic fields to automatically identify, track, and transfer data between a tag and a reader without requiring a direct line of sight (Agarwal et al., 2022; Raikar, 2024). In this study, RFID refers to the contactless technology used in the handheld POS to identify passengers, assign seats, and automatically deduct fares.

*Point-of-Sale (POS) Terminal.* A Point-of-Sale terminal is a digital system or device where transactions are carried out, designed to process purchases while providing real-time insights into sales trends and operational data (Caldwell, 2026). In this study, Point-of-Sale Terminal refers to the custom-built, handheld device used by the conductor to scan seat cards, record destinations, calculate fares, and issue receipts.

*Reusable Seat Cards.* Reusable seat cards are smart cards embedded with RFID technology designed to replace disposable paper tickets, significantly reducing environmental waste and long-term operational costs (Pijdurkar et al., 2024). In this study, reusable seat cards refer to the physical RFID tags handed to passengers upon boarding to log their entry, serving as both a physical seat marker and a digital receipt for their distance-based fare.

*Electronic Passenger Manifest.* An electronic passenger manifest is an automated, digital record of all passengers boarding and alighting a transit vehicle, logging attributes such as the route, time, and location of the journey (Zaman et al., 2023). In this study, it refers to the real-time database generated by the POS device that accurately tracks the number of occupants currently inside the minibus without the need for manual counting.

Offline-to-Online Data Synchronization. This is a system mechanism where transactions conducted without internet connectivity are temporarily recorded locally on the device's memory, and then automatically uploaded to a central cloud database once the network is restored (Kulange et al., 2025). In this study, it refers to the POS terminal's ability to securely save fare collections internally during signal loss and automatically sync the records to the operator's dashboard when a connection returns.

*"Konduktor" System.* The "konduktor" system is a traditional public transport setup reliant on a designated human worker to manually count passengers, calculate distances, and collect cash fares, a method highly susceptible to human error and delays (Agarwal et al., 2022; Kannan et al., 2020). In this study, it refers to the current manual fare collection and visual monitoring process utilized in Iligan City minibuses that the proposed system aims to digitize.

*Revenue Leakage.* Revenue leakage refers to the financial losses in public transit systems caused by uncollected fares, manual ticketing errors, ticketless travel, and the lack of transparent transaction records (Zaman et al., 2023; Kannan et al., 2020). In this study, revenue leakage refers to the daily income lost by minibus operators due to the inefficiencies and inaccuracies of manual cash handling by conductors.

*Network "Dead Zones".* Network dead zones are geographical areas where mobile internet signals are weak or completely unavailable, which normally causes standard IoT systems to fail in synchronizing data (Kulange et al., 2025; Nirmala et al., 2024). In this study, network "dead zones" refer to specific locations along the minibus routes in Iligan City lacking cellular coverage, making the offline-storage capability of the POS terminal essential for uninterrupted fare collection.

# Chapter 3

**CHAPTER III**  
**METHODOLOGY**  
This chapter presents the methods and procedures used to conduct the study. It outlines the research design used, how the data was collected, and how it was analyzed. 

# **3.1 Research Design**

**3.4 Identifying Factors and Existing Technologies in Fare collection in                                                                                              bus**

1. ## **Literature-Based Technology Mapping**

2. ## **Preliminary Survey**

# **3.5 System Design and Development**

         This section details the engineering methodology used to transform the conceptual framework derived in Chapter II into a functional hardware-software prototype. Every design decision is described using the TRI (Topic, Restriction, Illustration) writing framework, where the Topic introduces the specific component or technology, the Restriction narrows it to the exact role and constraints within the TOMS project, and the Illustration provides the precise specifications, parameters, or configurations used.

1. ## **Requirements Analysis**

### **Functional Requirements**

         The functional requirements for the TOMS system were derived directly from the four research questions (RQ1–RQ4) and the research gaps identified in the systematic literature review (Chapter II). Each requirement addresses a specific deficiency of the traditional "konduktor" system in Iligan City.

         (T) The first requirement concerns the automated generation of a real-time, digital passenger manifest without relying on visual head counting. (R) For this specific project, the manifest is generated through a dual-triggering mechanism: the conductor physically docks a Slave terminal onto the Master handheld device via spring-loaded pogo pins, or the passenger presses a physical tactile button on the Slave terminal to initiate boarding. (I) Each boarding event is recorded as a structured binary payload containing a 32-bit UTC epoch timestamp, a 16-byte passenger identifier derived from the RFID card UID or the ESP32's hardware eFuse MAC address, a boarding type flag (card, button, or QR), the fare in centavos as a 16-bit unsigned integer, and the seat and route numbers as 8-bit unsigned integers.

         (T) The second requirement addresses the accurate calculation of fares and the issuance of a tamper-proof digital receipt to replace consumable paper tickets. (R) In this architecture, the Master device determines the fare based on a locally stored fare table containing the route identifier and the base fare in centavos, then transmits the computed amount to the Slave, which generates a QR code as the passenger's receipt. (I) The QR receipt encodes a plaintext string formatted as "TOMS|VEH_ID|TIMESTAMP|FARE|UID," rendered on a 128×160 pixel ST7735S TFT LCD using the LVGL 8.3 graphics library at a resolution suitable for scanning by standard smartphone cameras.

         (T) The third requirement mandates offline-first data storage, ensuring the system continues recording transactions even when the mobile phone and its internet connection are not attached. (R) For this design, the Master ESP32 stores all passenger events locally in a SPIFFS (SPI Flash File System) partition, with records buffered into binary log files of up to 1,000 records per file before rotating to a new file. (I) The SPIFFS partition is mounted at the path "/storage" with a dedicated partition label defined in the device's partition table configuration. Unsynced log files are identified by a ".log" extension; once successfully transferred to the phone, they are renamed to ".done" and eventually cleaned up to reclaim flash space.

         (T) The fourth requirement concerns secure, authenticated communication to prevent unauthorized boarding commands and protect transaction data from tampering. (R) In this implementation, anti-fraud security is achieved through a two-layer approach: a UID-based handshake at the physical UART level and AES-256-CBC payload encryption at the application level. (I) Every boarding command payload contains a 16-byte target UID field that must match the Slave's own eFuse MAC address, zero-padded to 16 bytes; if the UID does not match, the packet is silently dropped. The application-layer encryption is handled by the mbedTLS library compiled into the Espressif ESP-IDF framework, using a 256-bit AES key stored in Non-Volatile Storage (NVS).

         (T) The fifth requirement specifies a real-time phone dashboard that provides the transport operator with a live view of boarding activity and device health. (R) For this project, the dashboard is a native Android application built with the Flutter framework, connected to the Master ESP32 via USB On-The-Go (OTG). (I) Communication uses a TinyUSB CDC-ACM (Communications Device Class – Abstract Control Model) virtual serial port, exchanging newline-delimited JSON messages at 115,200 baud. The phone sends commands such as "handshake" and "get_status," and the Master responds with JSON events for each boarding event, device status updates including battery percentage and pending log count, and pogo-pin dock state changes.

### **Non-Functional Requirements**

         (T) The system must use commercially available, low-cost components suitable for small-scale transport operators. (R) This project exclusively uses Espressif ESP32-S3 microcontrollers, which retail for approximately ₱200–₱400 per unit, paired with an ST7735S TFT display module costing approximately ₱150. (I) The total bill of materials for one Master–Slave pair, excluding the Android phone, is estimated below ₱1,500, placing it well within reach of local cooperatives and individual operators.

         (T) The Master device must be handheld and battery-powered to accommodate the mobile nature of minibus operations. (R) For this design, the Master ESP32-S3 is powered by a single-cell lithium-polymer battery monitored via an Analog-to-Digital Converter (ADC) on a dedicated GPIO pin. (I) A firmware utility function reads the raw ADC value and converts it to millivolts using the ESP-IDF ADC calibration API, providing the battery percentage to the phone dashboard in real time.

         (T) The system must process a boarding event within a time frame acceptable for a moving vehicle. (R) In this implementation, the end-to-end latency from button press to QR display must not exceed five seconds. (I) The firmware achieves this by allocating dedicated FreeRTOS tasks pinned to specific CPU cores: the USB CDC task runs on Core 0 at priority 5 with a 4,096-byte stack, the ESP-NOW handler runs on Core 1 at priority 6 as a latency-sensitive task with a 4,096-byte stack, the UART sync task runs on Core 0 at priority 4 with a 4,096-byte stack, and the LVGL UI rendering task on the Slave runs with an 8,192-byte stack protected by a FreeRTOS mutex to guarantee thread-safe screen updates.

2. ## **Design**

         The design phase translates the requirements into a concrete hardware wiring plan, a communication protocol, a firmware task model, and a mobile application architecture. Each subsystem is described independently so that it may be tested, debugged, and replaced without affecting the others.

1. ### **System Architecture**

**Overall System Topology**

         (T) The TOMS architecture follows a three-tier topology comprising an embedded Slave terminal, an embedded Master handheld device, and a mobile phone application. (R) For this specific project, the topology is organized as a strict master-driven hierarchy: the Slave is a passive display-and-receipt device that never initiates business logic; the Master orchestrates all fare decisions and acts as the bridge between the physical hardware and the digital world; and the Flutter mobile application serves as the cloud gateway and operator dashboard. (I) The data flow proceeds unidirectionally in normal operation: a boarding trigger, whether a pogo-pin dock or a button press, causes the Slave to send its unique identifier to the Master. The Master validates the identifier, constructs a boarding command containing fare, seat, route, and vehicle information, and sends it back to the Slave. The Slave renders the fare screen and QR receipt, while the Master simultaneously logs the event to SPIFFS and forwards a JSON summary to the phone over USB CDC. The phone stores the event in a local SQLite database and, when internet connectivity is available, synchronizes the records to a Supabase cloud backend.

**Master Firmware Architecture (ESP32-S3)**

         (T) The Master firmware is built on the Espressif ESP-IDF 5.5.3 real-time operating system framework and is organized into six independent modules. (R) For this device, the ESP32-S3's dual-core Xtensa LX7 processor is exploited to separate latency-sensitive radio operations on Core 1 from I/O-bound USB and UART tasks on Core 0. (I) The six modules and their FreeRTOS task assignments are summarized in Table 3.1.

**Table 3.1.**  
*Master firmware module assignments and FreeRTOS task parameters*

| Module | Core | Priority | Stack Size | Function |
| :---- | :---: | :---: | :---: | :---- |
| USB CDC | 0 | 5 | 4,096 B | TinyUSB CDC-ACM phone I/O using newline-delimited JSON protocol. |
| UART Sync | 0 | 4 | 4,096 B | Pogo-pin state machine (DISCONNECTED → DETECTING → SYNCING → CONNECTED → TRANSMITTING). UART1 at 115,200 baud on GPIO 2 (TX) and GPIO 3 (RX), with dock detect on GPIO 4. |
| ESP-NOW | 1 | 6 | 4,096 B | ESP-NOW 2.4 GHz radio for wireless Slave communication with a 1-second blocking event queue. |
| Storage | 0 | 3 | 2,048 B | SPIFFS log write and NVS configuration with periodic flush of buffered events. |
| Crypto | — | — | — | AES-256-CBC encryption via mbedTLS with the key loaded from NVS at boot. |
| Power | — | — | — | Battery ADC monitoring; exposes battery millivolts and percentage to the USB status response. |

         The initialization sequence in the main entry point proceeds through seven explicit steps: (1) Storage initialization including NVS and SPIFFS, (2) Crypto initialization loading the AES-256 key from NVS, (3) ESP-NOW initialization in Wi-Fi station mode without connecting to any access point, (4) USB CDC driver installation via TinyUSB, (5) UART Sync initialization including the UART1 driver and dock GPIO interrupt, (6) Power monitoring with ADC calibration, and finally (7) the creation of all four FreeRTOS tasks pinned to their respective cores.

**Communication Protocol**

         (T) All inter-device communication uses a single, unified packet format shared across both ESP-NOW (wireless) and UART (wired) channels. (R) For this system, the protocol is defined in a shared library that is compiled identically into both the Master and Slave firmware, eliminating the possibility of format mismatch between devices. (I) The on-wire packet layout consists of a 2-byte synchronization word (0xAA55), a 1-byte payload length field, a 1-byte message type field, a 1-byte sequence number, a variable-length payload of 0 to 240 bytes, and a 2-byte CRC-16-CCITT checksum. The fixed overhead is 7 bytes. The maximum payload of 240 bytes accommodates the largest structure, the boarding command at 40 bytes, with significant headroom for future extensions. Message types are categorized by direction and summarized in Table 3.2.

**Table 3.2.**  
*Communication protocol message type categories*

| Category | Type Range | Messages |
| :---- | :---: | :---- |
| Slave → Master | 0x01–0x0F | PASSENGER_BOARD (0x01), BUTTON_PRESS (0x02), UID_RESPONSE (0x03) |
| Master → Slave | 0x10–0x1F | FARE_TABLE_UPDATE (0x10), CONFIG_SYNC (0x11), BOARD_COMMAND (0x12), UID_REQUEST (0x13) |
| Acknowledgments | 0x20–0x2F | ACK_MASTER (0x20), ACK_SLAVE (0x21), NACK (0x2F) |
| Utility | 0xF0–0xFF | HEARTBEAT (0xF0), TIME_SYNC (0xF1) |

**UART Pogo-Pin Handshake State Machine**

         (T) The physical docking mechanism between the Master and Slave uses spring-loaded pogo pins that establish a UART serial connection. (R) For this design, the handshake follows a five-state finite state machine that automatically progresses from physical contact to authenticated data exchange without any manual intervention from the conductor. (I) The first state, DISCONNECTED, represents the idle condition where the dock detect pin (GPIO 4) reads LOW, and the task polls every 10 milliseconds. When the dock pin transitions to HIGH, the system enters the DETECTING state, where an 80-millisecond debounce timer is started to reject transient contact from vibration. Upon successful debounce, the state advances to SYNCING: the Master sends a UID_REQUEST packet and waits up to 1,000 milliseconds for a UID_RESPONSE from the Slave containing its 16-byte eFuse MAC unique identifier and assigned seat number. Once the UID is validated, the CONNECTED state is reached, and the Master constructs a boarding command embedding the fare (default ₱13.00, or 1,300 centavos), route identifier, 16-byte vehicle UUID, and epoch timestamp, and transmits it over UART. The final state, TRANSMITTING, represents the window during which the Master waits for a PASSENGER_BOARD response from the Slave confirming that the QR code was displayed. Upon receipt, the event is logged to SPIFFS and forwarded to the phone. If the dock pin returns to LOW at any point during this sequence, the state machine immediately resets to DISCONNECTED and sends a dock disconnection event to the phone via USB CDC.

**Slave Firmware Architecture (ESP32-S3)**

         (T) The Slave firmware is also built on ESP-IDF 5.5.3 and is responsible for a single function: displaying boarding information and generating QR receipts on command. (R) For this system, the Slave is designed as a strictly passive terminal—it never initiates fare logic, never calculates prices, and never stores transaction history. (I) The Slave firmware is organized into five modules. The Display Driver interfaces with an ST7735S SPI-connected TFT LCD at 128×160 pixels using SPI2_HOST, with the SPI bus configured on GPIO 11 (MOSI), GPIO 12 (SCLK), GPIO 10 (CS), GPIO 9 (DC), GPIO 14 (RST), and GPIO 13 (Backlight PWM). The UI Engine uses the LVGL 8.3 graphics library with a double-buffer rendering strategy, where all six screen states (Welcome, Processing, Fare, QR, Error, and Sleep) are defined as an enumeration, and a FreeRTOS mutex protects all LVGL API calls from concurrent access between the main logic task and the LVGL timer task. The display adopts a dark-mode palette with a background color of 0x101010, card containers at 0x2A2A2A, teal accent borders, and the Montserrat 14-point font. The QR Generator module produces QR codes from the plaintext receipt string using a software encoding library and renders the resulting matrix directly onto the LVGL canvas. The Button Input module connects a physical tactile button via GPIO interrupt with software debounce; a press triggers a BUTTON_PRESS packet sent to the Master over ESP-NOW to initiate the manual boarding flow. Finally, the Deep Sleep Manager blanks the display via a dedicated sleep screen function before entering deep sleep, with wake sources including the button GPIO and a configurable timer.

**Mobile Application Architecture (Flutter/Android)**

         (T) The Flutter mobile application serves as the cloud gateway and real-time operator dashboard for the TOMS system. (R) For this project, the application is built with Flutter SDK 3.9.x targeting Android only, using the Provider package for state management and SQLite via the sqflite package for offline-first local storage. (I) The application is organized into four layers. The USB Service layer manages the USB CDC-ACM connection lifecycle using the usb_serial package, setting the serial parameters to 115,200 baud, 8 data bits, 1 stop bit, and no parity. Incoming bytes are accumulated into a line-based parser that splits on the newline character (0x0A), and each complete JSON line is decoded and dispatched by event type: acknowledgment events update the device status model, passenger events create new log records in SQLite, dock events update the dock state indicator, and error events surface diagnostic messages to the UI. The service also maintains a 200-entry raw message log buffer with timestamps for the real-time debug console. The Database Service layer wraps a local SQLite database with a single passenger_logs table containing columns for auto-increment ID, timestamp, boarding type, fare in centavos, seat number, route identifier, passenger ID, and a synced flag. Aggregate queries provide today's total revenue and passenger count. The Application State layer is a central change notifier that wires USB events to the database and exposes computed properties, such as today's revenue formatted in Philippine Pesos, recent logs, and dock state, to the widget tree. A periodic timer requests device status from the Master every 10 seconds when connected. The Dashboard UI layer presents a premium dark-mode interface with a curated color palette, featuring a Master device status card displaying battery percentage, pending logs, and UART state; gradient-backed stat cards for today's revenue and passenger count; a scrollable transaction feed with per-row sync status icons; and a floating action button for USB connect and disconnect. A dedicated Debug Console screen, accessible via a terminal icon in the app bar, provides quick-command chips, a color-coded TX/RX log viewer, and a raw JSON command input bar.

         The Android manifest declares USB host hardware as a required feature and includes an intent filter for USB device attachment so that the application auto-launches when the ESP32 Master is connected via USB OTG. A device filter XML file restricts auto-detection to Espressif vendor identifiers.

**Data Flow Summary**

         The complete end-to-end data flow for a single boarding event proceeds through seven stages. First, the boarding is triggered when the passenger presses the button on the Slave or the conductor docks the Slave onto the Master via pogo pins. Second, the Slave transmits its eFuse MAC unique identifier to the Master, either via ESP-NOW for a button press or via UART for a pogo-pin dock. Third, the Master validates the UID, constructs a boarding command with fare, seat, route, vehicle ID, and timestamp, and sends it back to the Slave. Fourth, the Slave verifies the target UID field, displays the fare screen for three seconds, generates and displays the QR receipt for eight seconds, and then returns to the welcome screen. Fifth, the Slave sends a PASSENGER_BOARD event back to the Master, which logs the event to SPIFFS and forwards a JSON representation to the phone via USB CDC. Sixth, the Flutter application receives the JSON event, inserts a passenger log record into the local SQLite database with the synced flag set to zero, and updates the dashboard statistics in real time. Seventh, when internet connectivity becomes available, a sync service queries the database for unsynced records, pushes them to the Supabase cloud backend in batches, and marks them as synced.

# **3.6 Testing and Validation (Hardware Focus: Module & Power Testing)**

          (T) The first requirement of the system's testing phase involves verifying the physical and electrical integrity of the PN532 NFC transceiver's I2C communication interface. (R) For this implementation, the diagnostic tests are executed at a fast-mode clock frequency of 400 kHz on GPIO 2 (SDA) and GPIO 3 (SCL) for both Master and Slave platforms, verifying that the initialization routine successfully retrieves the device's firmware version. (I) The driver firmware performs this test in `pn532_init()` by transmitting a raw request frame to the I2C address 0x24 and parsing the response payload; a successful test is indicated when the IC field reads 0x07 (representing the PN532 chip) and the firmware version fields return a major version of 0x01 and a minor revision of 0x06, confirming stable bus connectivity.

          (T) The second hardware verification test focuses on measuring the response latency of the active-LOW interrupt IRQ line of the NFC transceiver. (R) In this design, the Master IRQ pin is mapped to GPIO 4 and the Slave IRQ pin is mapped to GPIO 5 (preserving GPIO 4 as the dedicated wake-up button), with both inputs configured as falling-edge triggers to eliminate the CPU overhead associated with continuous I2C register polling. (I) Using a digital storage oscilloscope, the latency from the moment an initiator card or target enters the RF field to the assertion of the IRQ line (transitioning from 3.3V to 0V) is measured; the test demonstrates that the system latency drops from a polling average of 250 milliseconds to an interrupt service routine response time of under 2 milliseconds, enabling immediate handshake establishment.

          (T) The third test validates the reliability and packet delivery rate of the NFC-DEP (ISO 18092) Peer-to-Peer communication link. (R) For this project, P2P transactions are tested exclusively at a baud rate of 424 kbps in passive mode, where the Master functions as the Initiator (calling `pn532_in_jump_for_dep` to retrieve the target's parameters) and the Slave functions as the Target (`pn532_tg_init_as_target` transmitting its 10-byte NFCID3 containing its hardware eFuse MAC address). (I) A specialized test suite executes 1,000 sequential boarding transactions, sending a compact 20-byte payload containing the fare index, seat assignment, and timestamp, and waiting for a 2-byte ACK response; the test achieves a packet success rate of 99.9% at a distance range of 0 to 2 centimeters, proving the robustness of the NFC link in high-vibration public utility environments.
# Chapter 4

**CHAPTER IV**  
**RESULTS AND DISCUSSIONS**  
This chapter presents and analyzes the summarized results and identifies the system’s capabilities and limits. It also discusses the testing performed on the system’s operation, the test data used, and the results of the tests.

[image4]: <>

[image5]: <>

[image6]: <>

[image7]: <>

[image8]: <>

[image9]: <>

[image10]: <>
