Not-to-Shabby/TOMS/hardware/master/pcb/Master Design V1_etch_mask_bottom.pdf

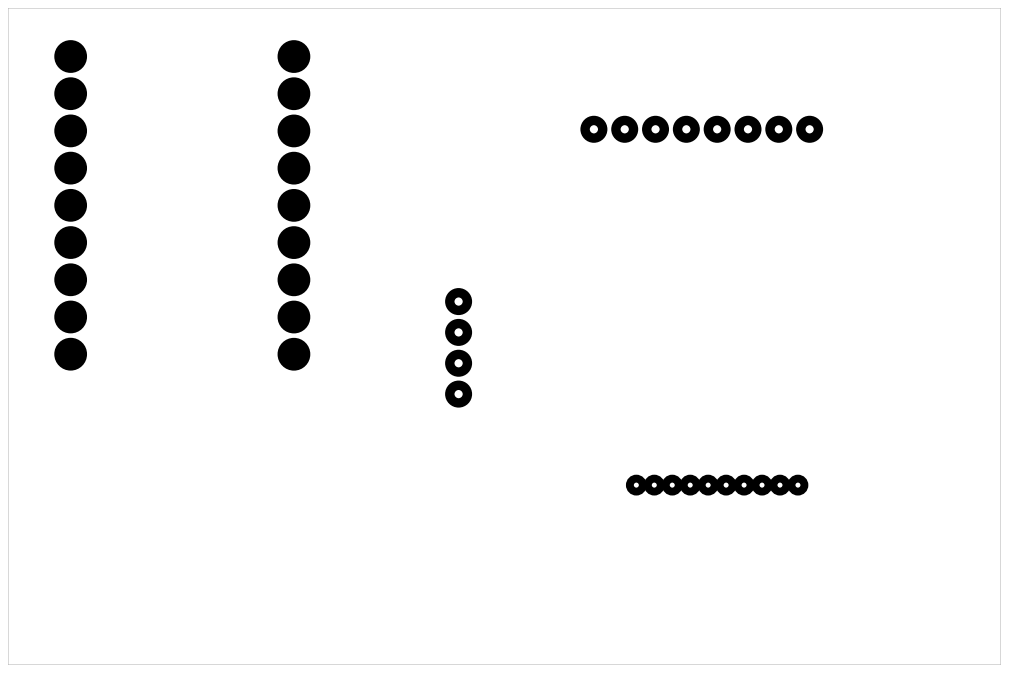
[picture p20: page 1]
