Not-to-Shabby/TOMS/hardware/master/pcb/Master Design V1_etch_mask_bottom_mirror.pdf

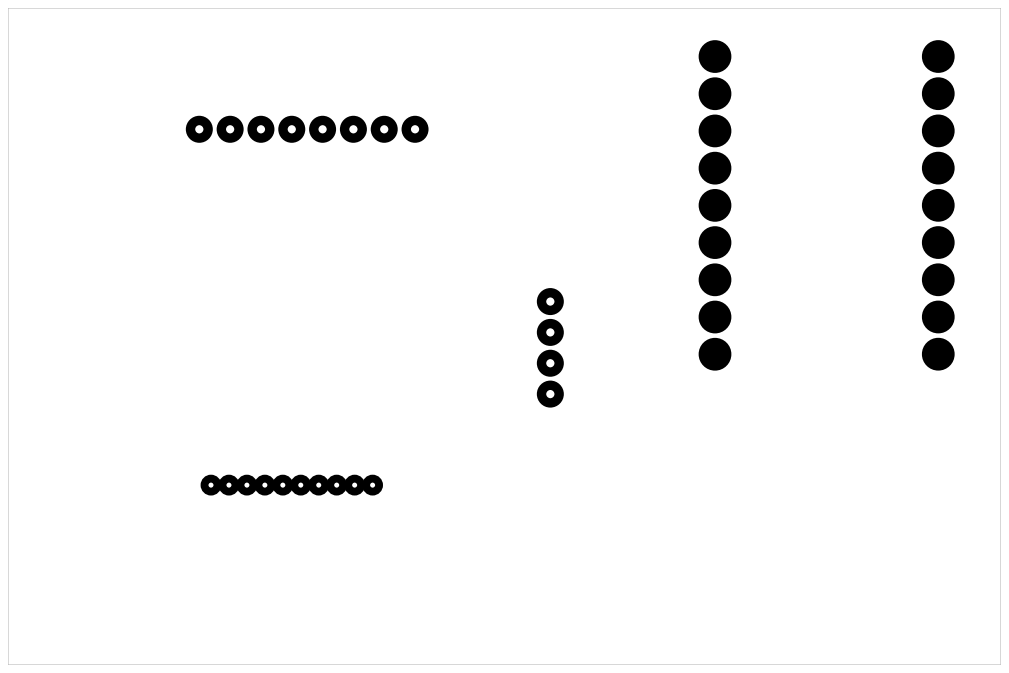
[picture p21: page 1]
