Not-to-Shabby/TOMS/hardware/master/pcb/Master Design V1_etch_silk_bottom.pdf

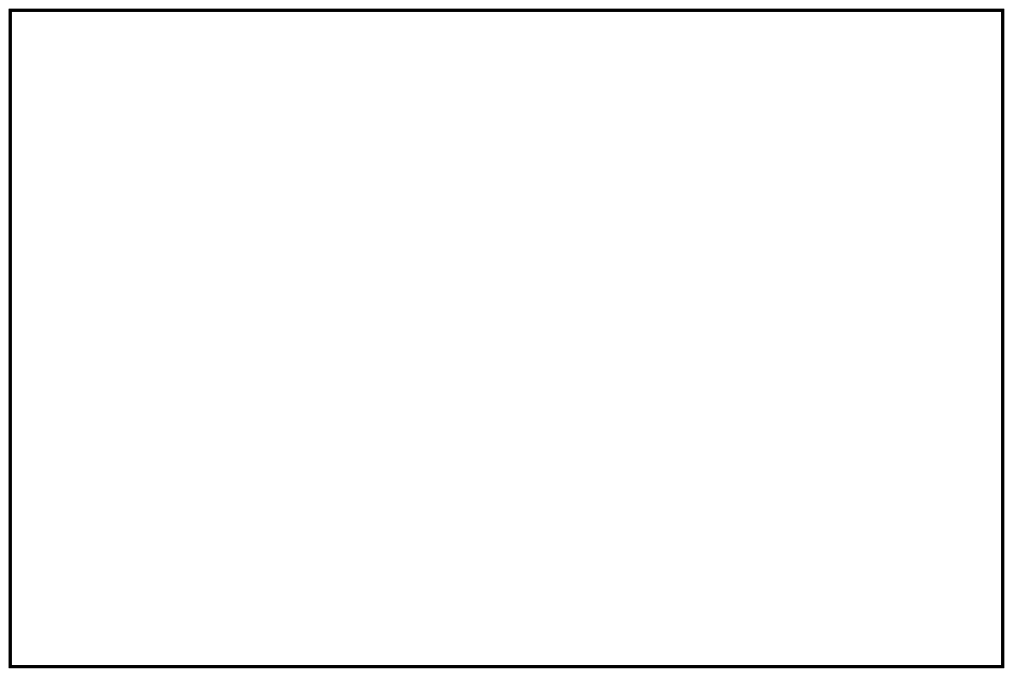
[picture p22: page 1]
