Not-to-Shabby/TOMS/hardware/master/pcb/Master Design V1_etch_silk_bottom_mirror.pdf

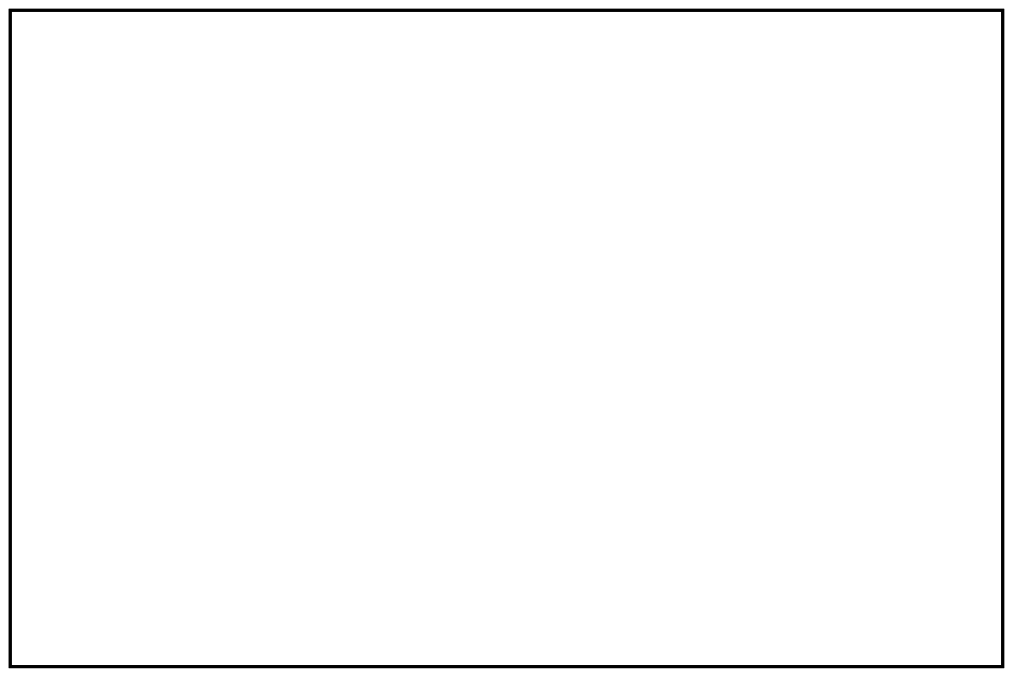
[picture p23: page 1]
