Not-to-Shabby/TOMS/hardware/master/pcb/Master Design V1_etch_silk_top.pdf

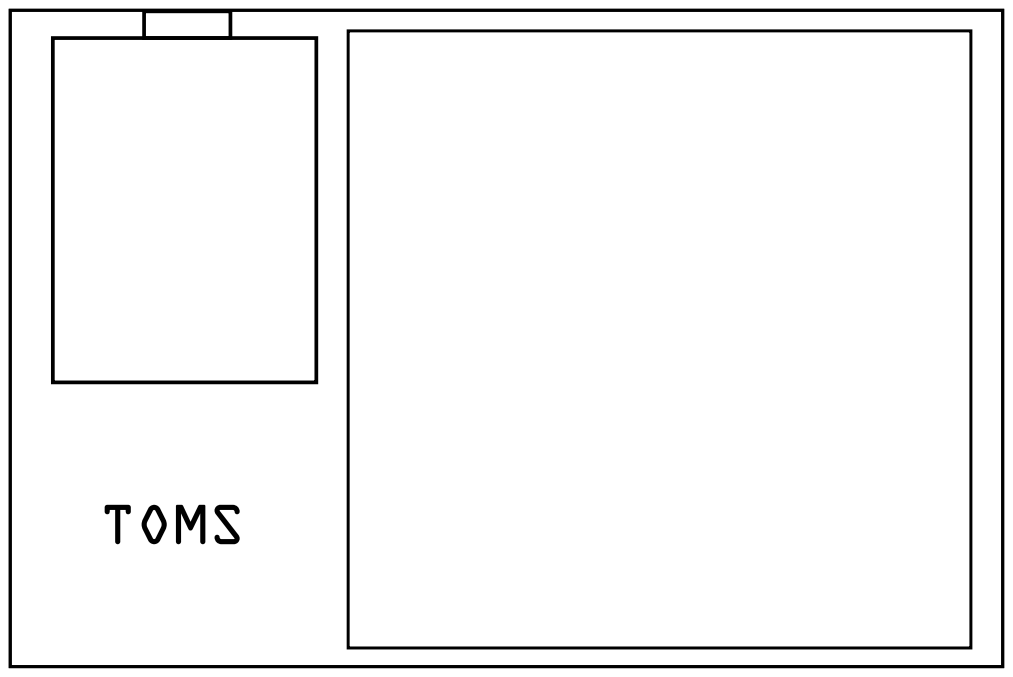
[picture p24: page 1]
