Not-to-Shabby/TOMS/hardware/master/pcb/Master Design V1_etch_silk_top_mirror.pdf

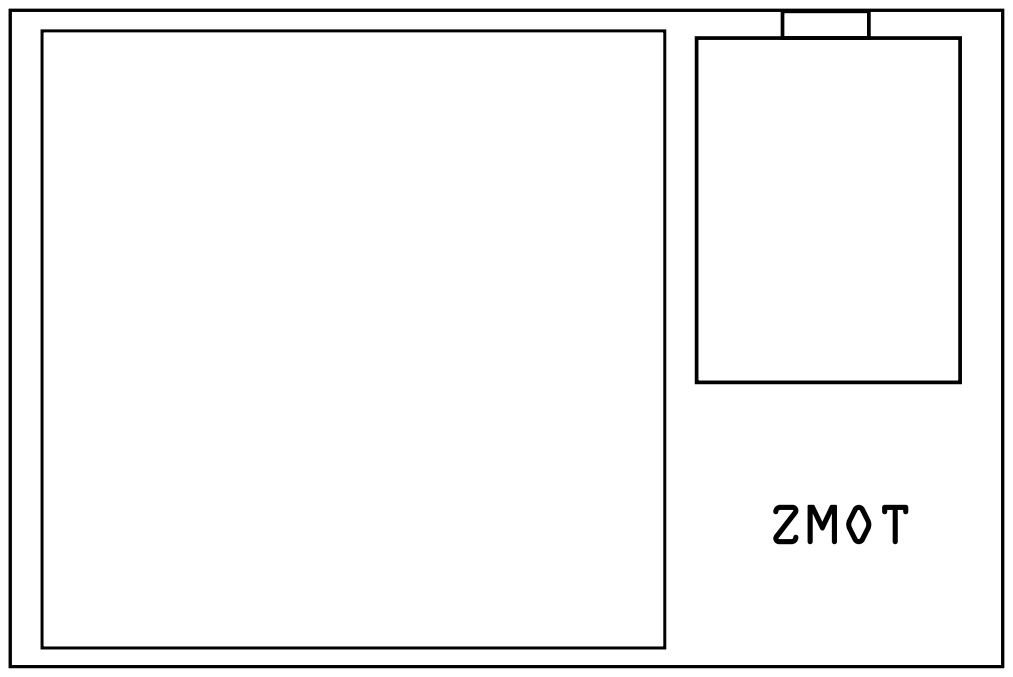
[picture p25: page 1]
