Not-to-Shabby/TOMS/hardware/slave/pcb/Slave Design v2.1_etch_copper_bottom.pdf

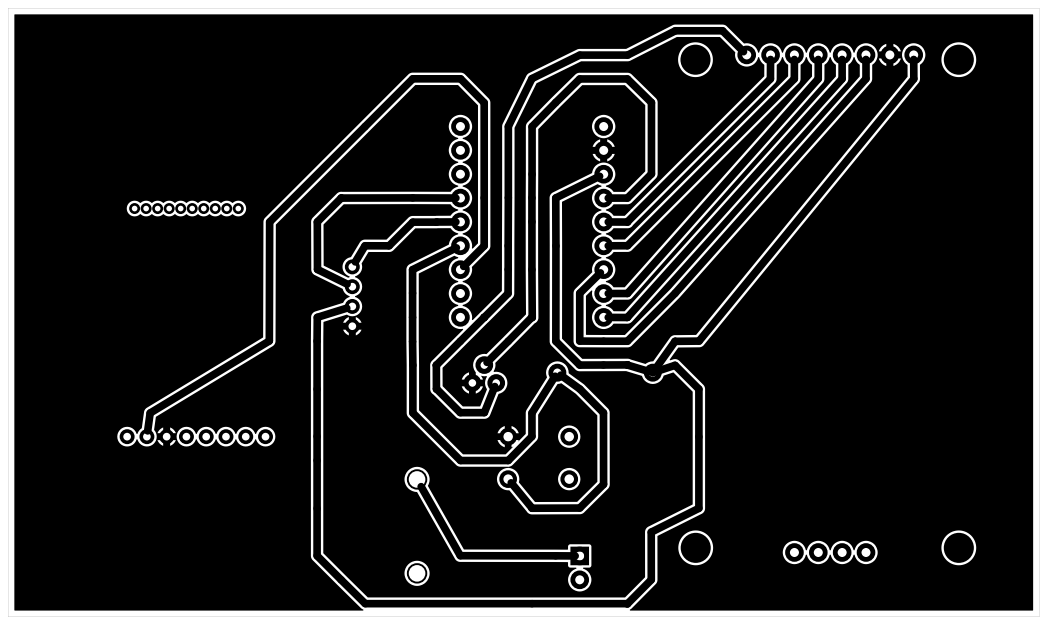
[picture p26: page 1]
