Not-to-Shabby/TOMS/hardware/slave/pcb/Slave Design v2.1_etch_copper_bottom_mirror.pdf

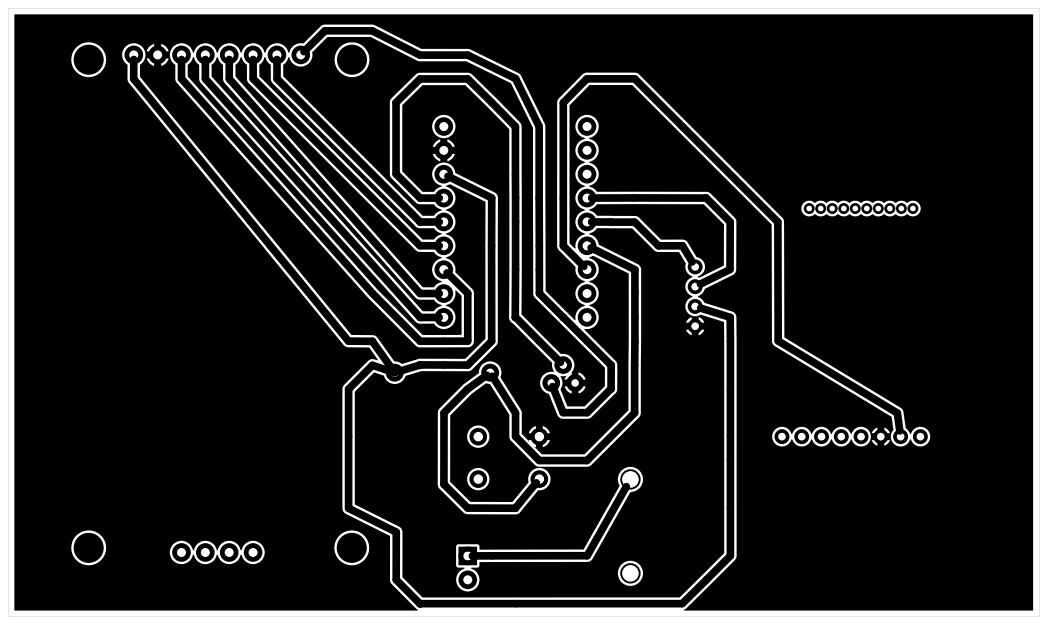
[picture p27: page 1]
