Not-to-Shabby/TOMS/hardware/slave/pcb/Slave Design v2.1_etch_mask_bottom.pdf

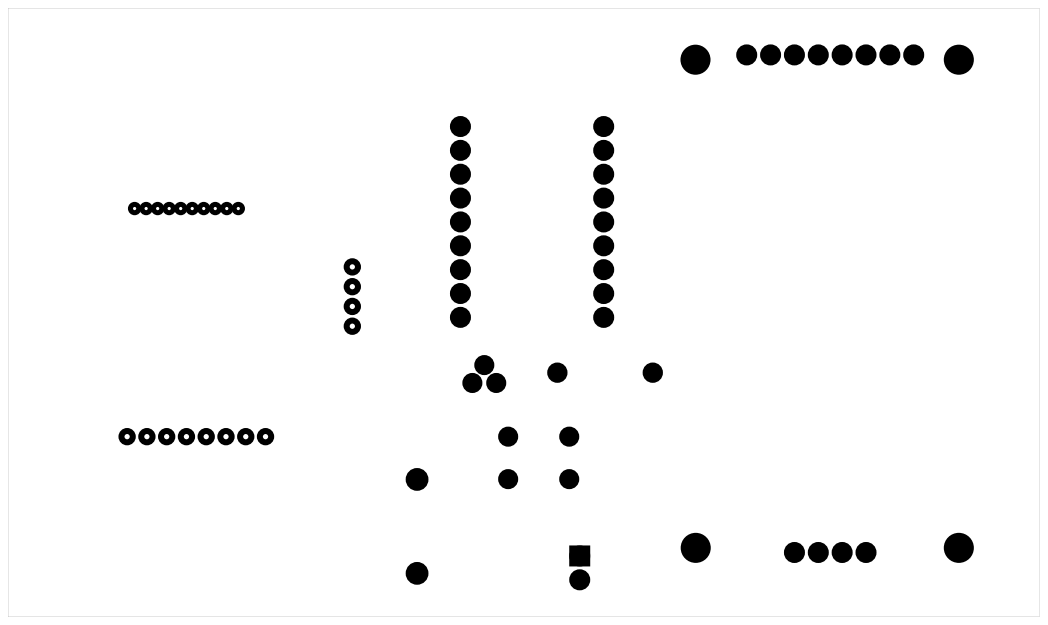
[picture p28: page 1]
