Not-to-Shabby/TOMS/hardware/slave/pcb/Slave Design v2.1_etch_mask_bottom_mirror.pdf

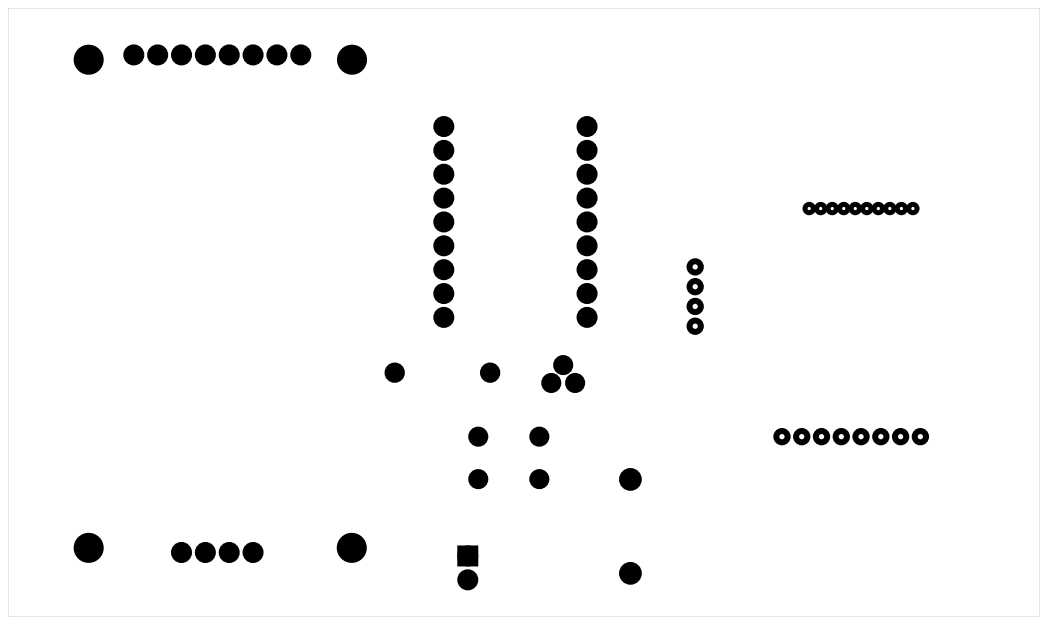
[picture p29: page 1]
