Not-to-Shabby/TOMS/hardware/slave/pcb/Slave Design v2.1_etch_silk_top.pdf

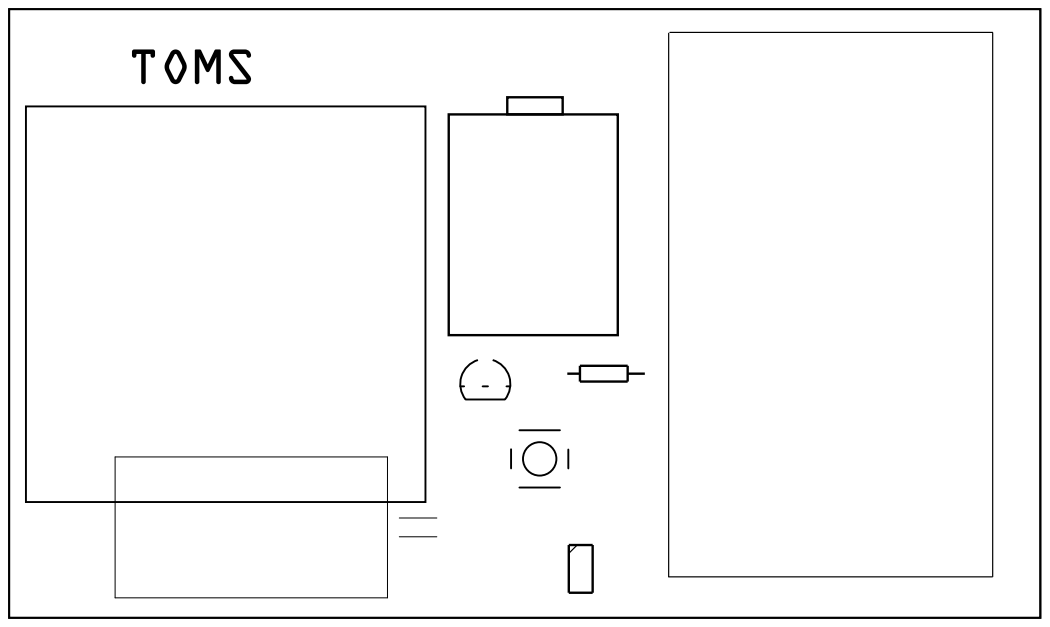
[picture p30: page 1]
