Not-to-Shabby/TOMS/hardware/slave/pcb/Slave Design v2.1_etch_silk_top_mirror.pdf

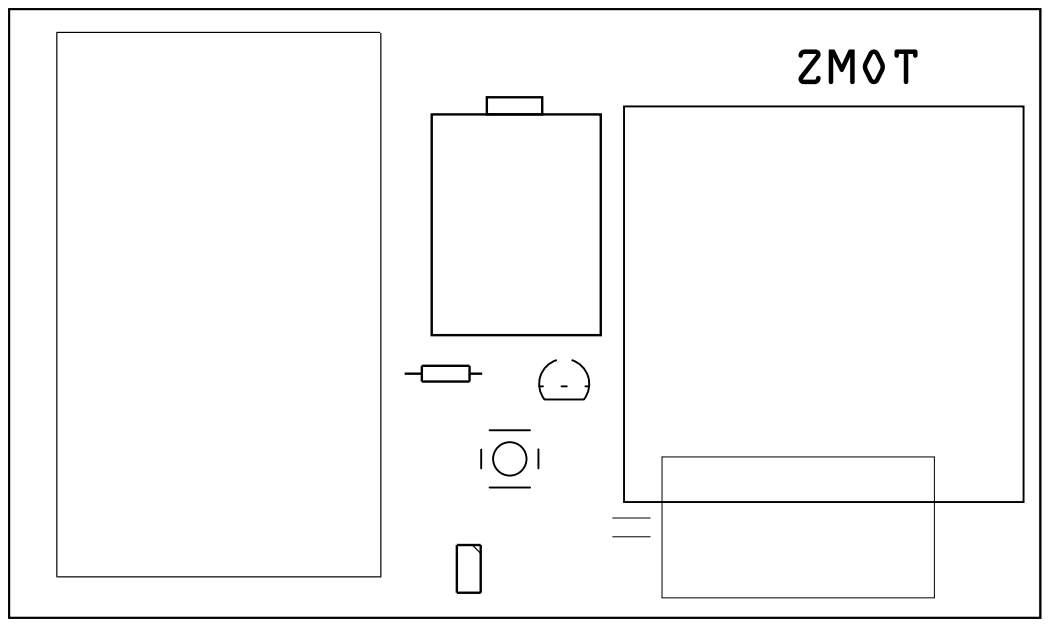
[picture p31: page 1]
